arjenhiemstra/ithowifi/images/itho pcb w add-on.png

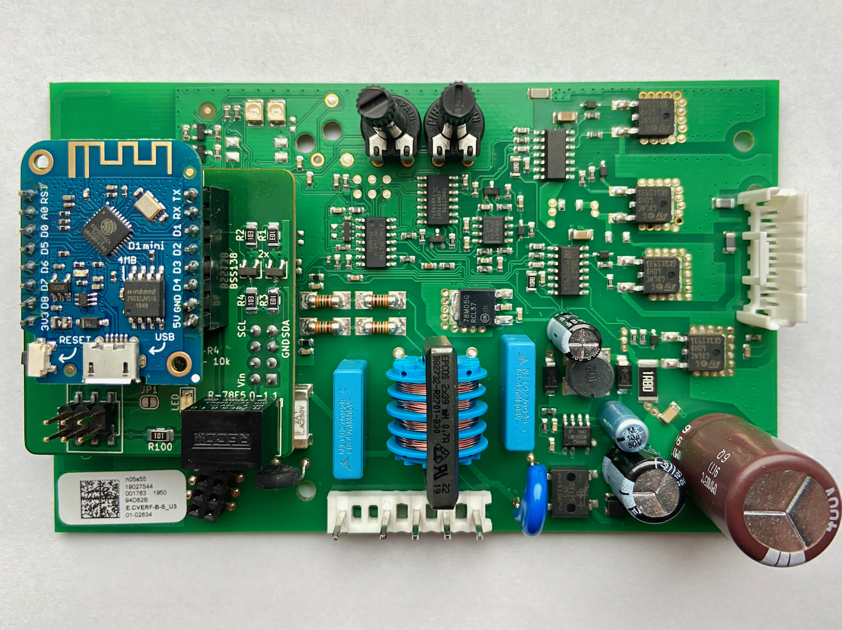
images/itho pcb w add-on.png
