arjenhiemstra/ithowifi/images/itho pcb.png

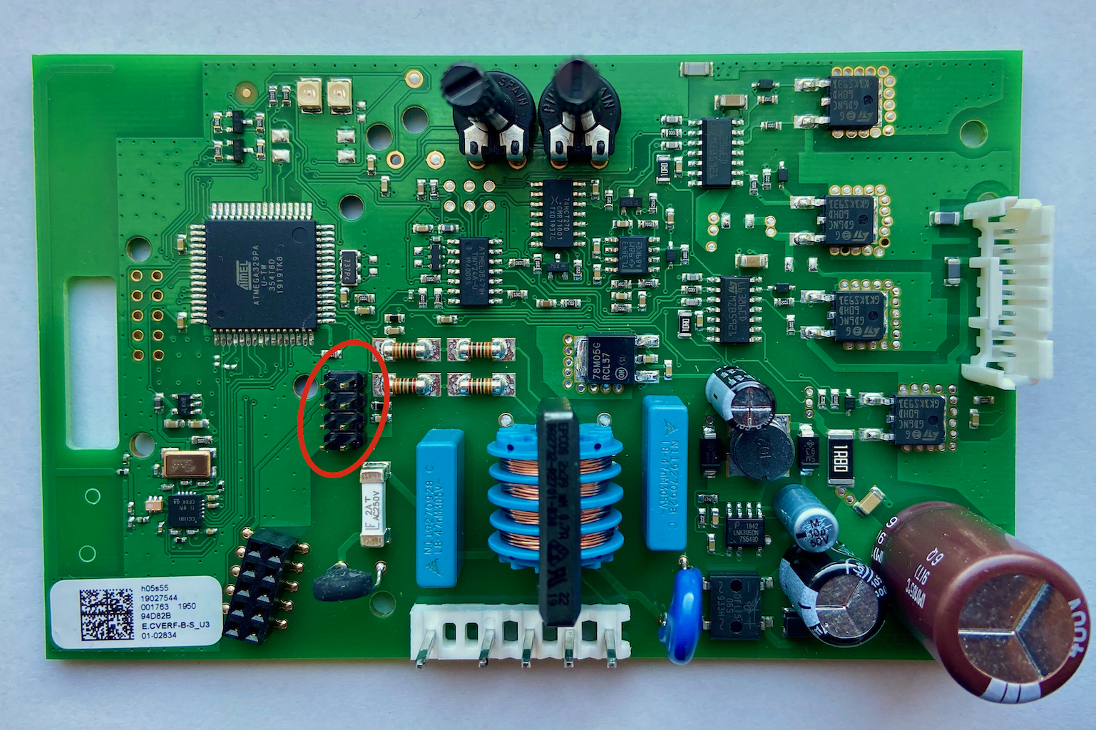
images/itho pcb.png
