arjenhiemstra/ithowifi/images/wiki/HRU pins.jpg

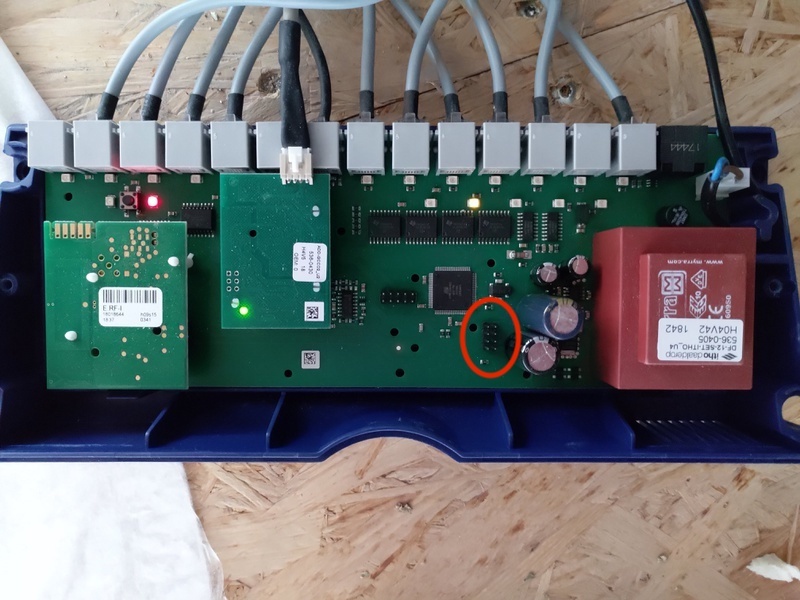
images/wiki/HRU pins.jpg
