arjenhiemstra/ithowifi/images/wiki/itho_grey_box.jpg

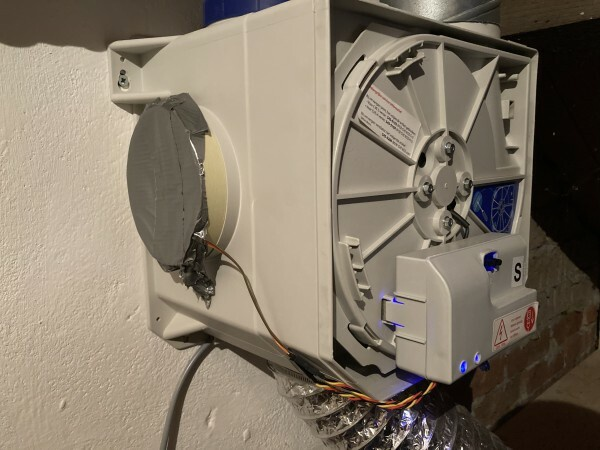
images/wiki/itho_grey_box.jpg
