arjenhiemstra/ithowifi/images/wiki/itho_in_blue_box.jpg

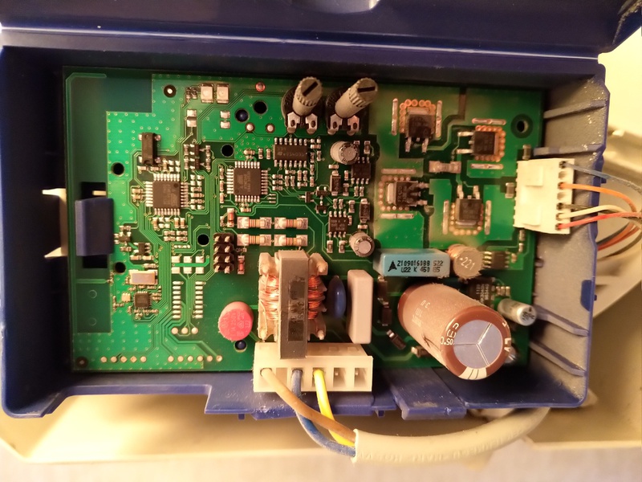
images/wiki/itho_in_blue_box.jpg
