arjenhiemstra/ithowifi/images/wiki/itho_RV_through-hole-box.jpg

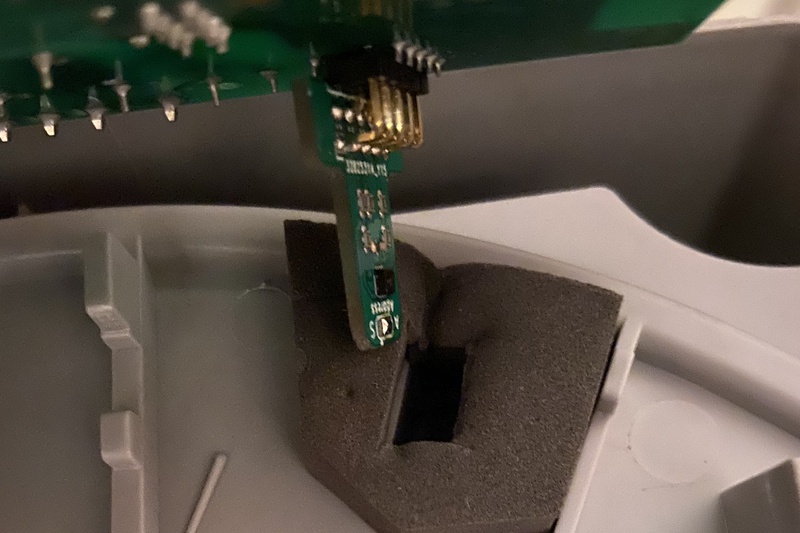
images/wiki/itho_RV_through-hole-box.jpg
