arjenhiemstra/ithowifi/images/wiki/join command.jpg

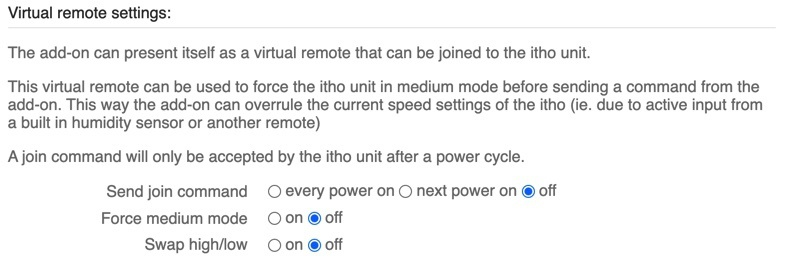
images/wiki/join command.jpg
