arjenhiemstra/ithowifi/images/wiki/pcb.png

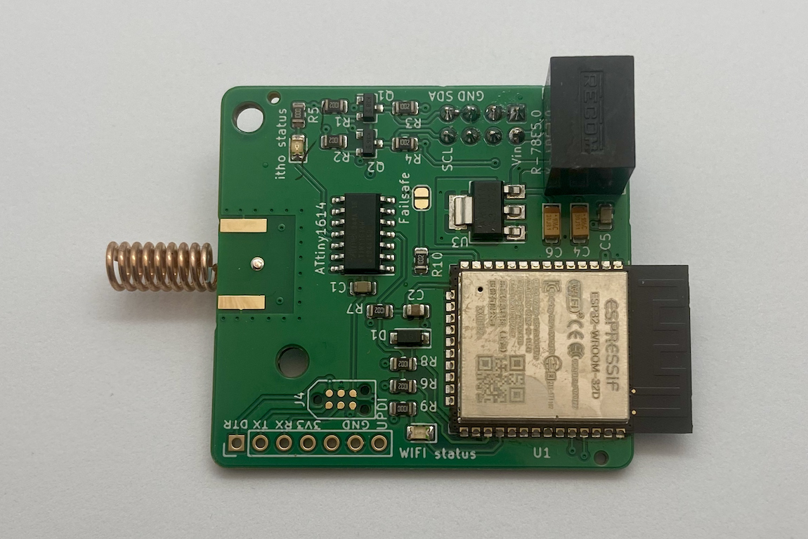
images/wiki/pcb.png
