arjenhiemstra/ithowifi/images/wiki/pinout rv sensor.png

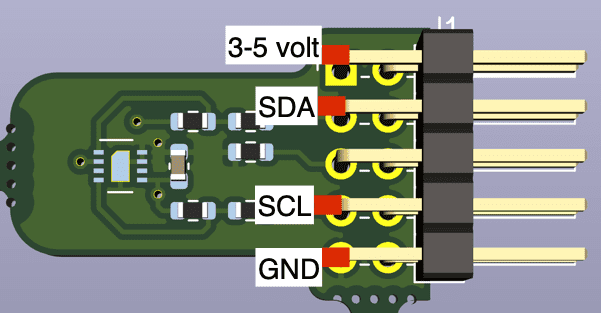
images/wiki/pinout rv sensor.png
