arjenhiemstra/ithowifi/images/wiki/Possible RV location2.jpg

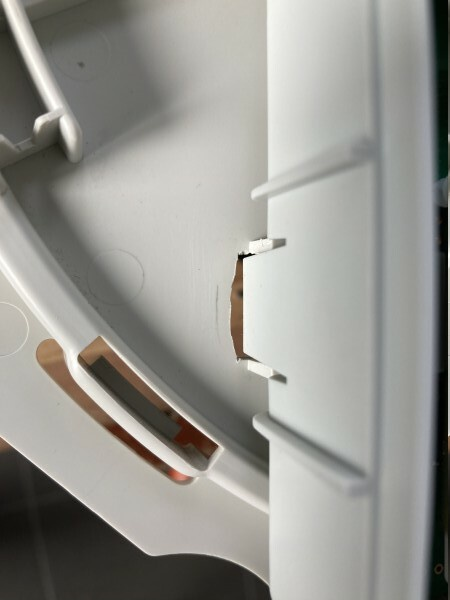
images/wiki/Possible RV location2.jpg
