arjenhiemstra/ithowifi/images/wiki/Possible RV location3.jpg

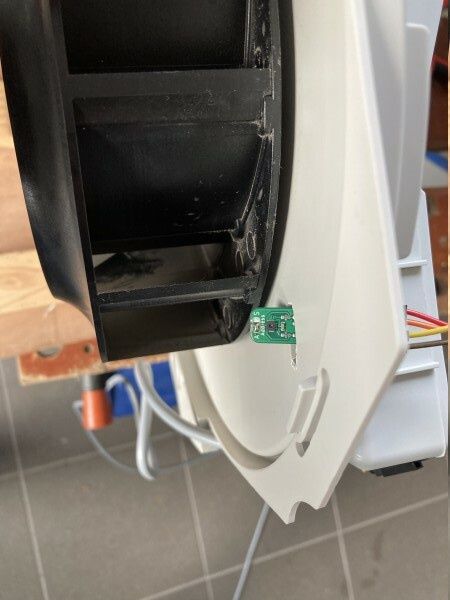
images/wiki/Possible RV location3.jpg
