arjenhiemstra/ithowifi/images/wiki/Possible RV location4.jpg

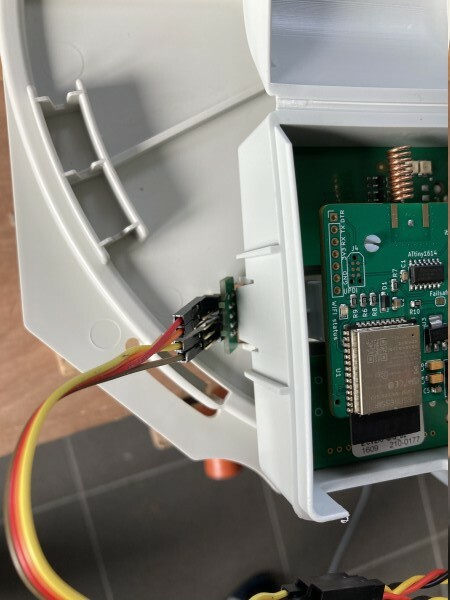
images/wiki/Possible RV location4.jpg
