arjenhiemstra/ithowifi/images/wiki/Remote 1.jpg

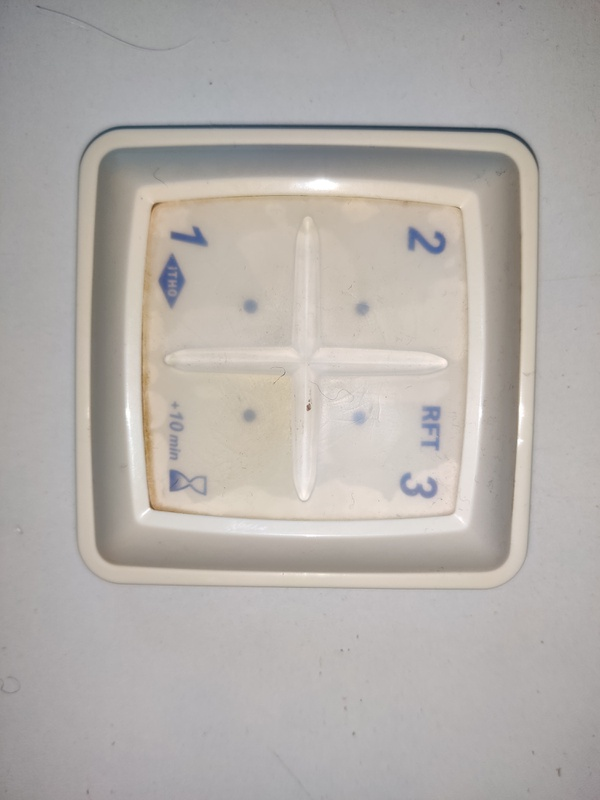
images/wiki/Remote 1.jpg
