arjenhiemstra/ithowifi/images/wiki/Remote 1_inside_bottom.jpg

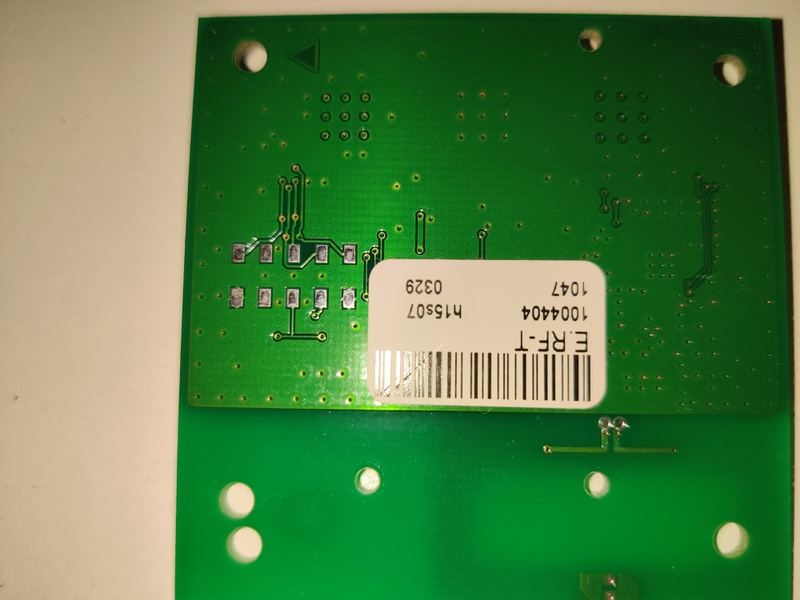
images/wiki/Remote 1_inside_bottom.jpg
