arjenhiemstra/ithowifi/images/wiki/Remote 1_inside_top.jpg

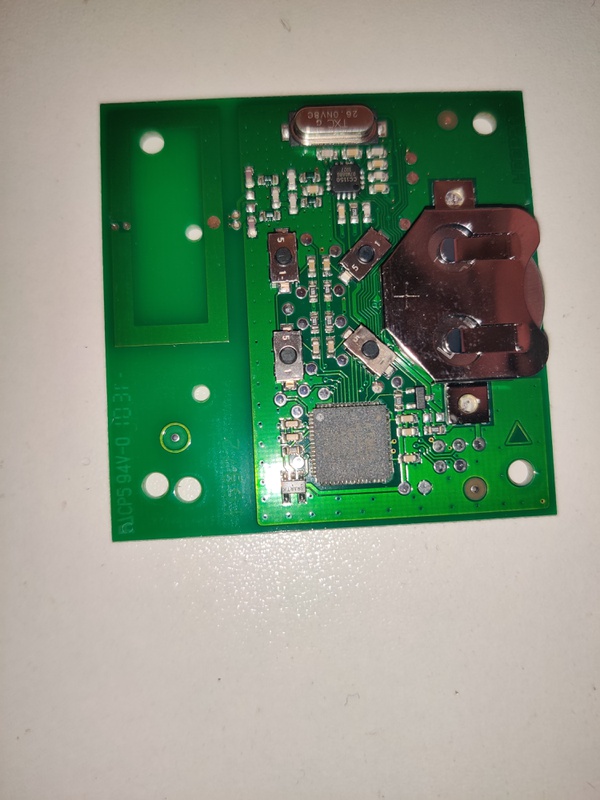
images/wiki/Remote 1_inside_top.jpg
