arjenhiemstra/ithowifi/images/wiki/Remote 2.jpg

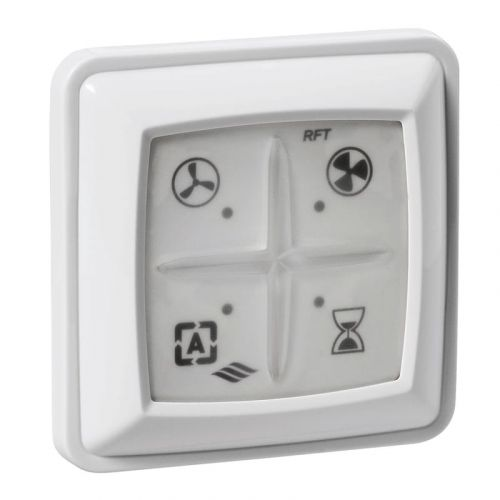
images/wiki/Remote 2.jpg
