arjenhiemstra/ithowifi/images/wiki/RV (org left) replacement (right).jpg

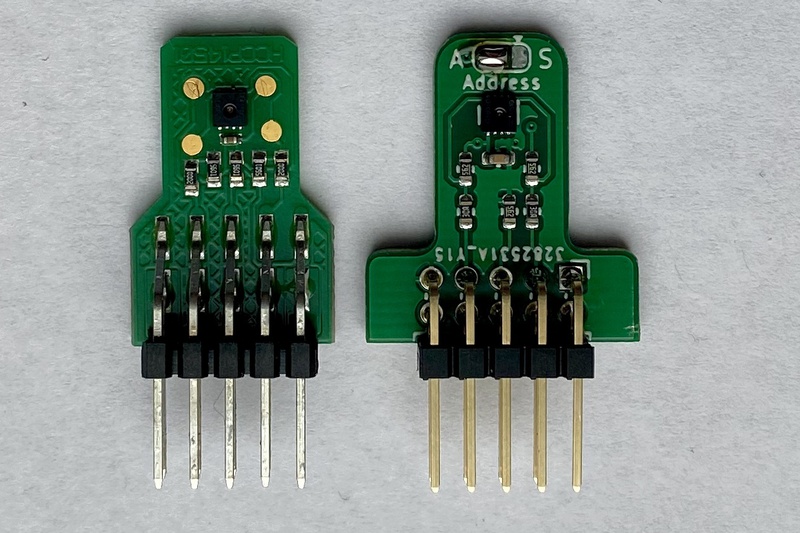
images/wiki/RV (org left) replacement (right).jpg
