arjenhiemstra/ithowifi/images/wiki/RV_bottom_side.jpg

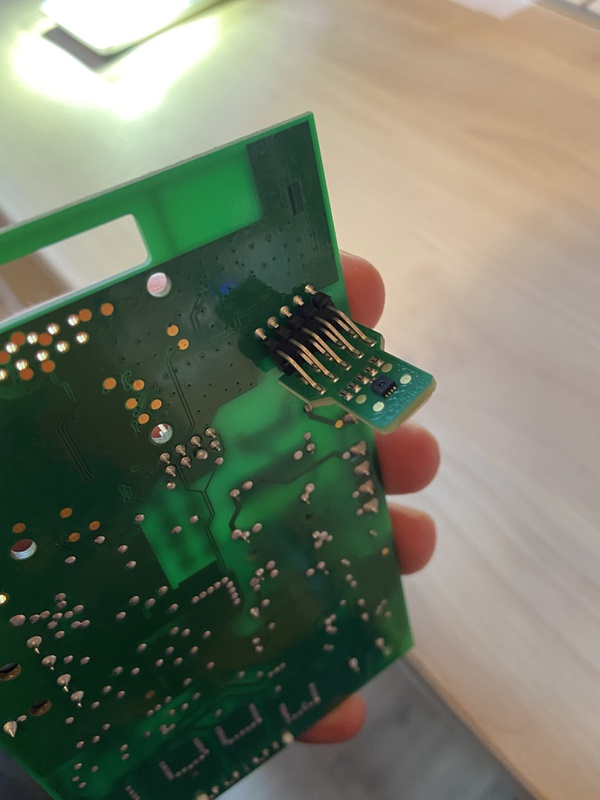
images/wiki/RV_bottom_side.jpg
