arjenhiemstra/ithowifi/images/wiki/speedsetting fan software.jpg

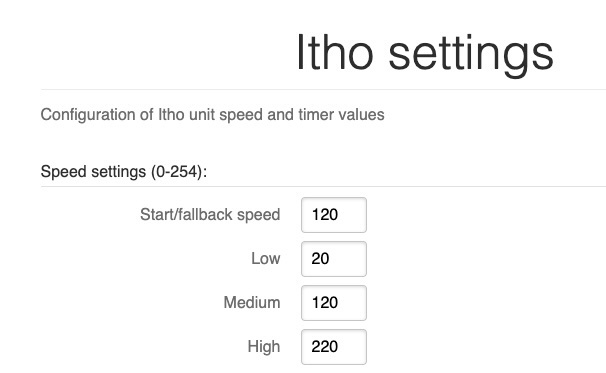
images/wiki/speedsetting fan software.jpg
