arjenhiemstra/ithowifi/images/wiki/sticker_from Factory.jpg

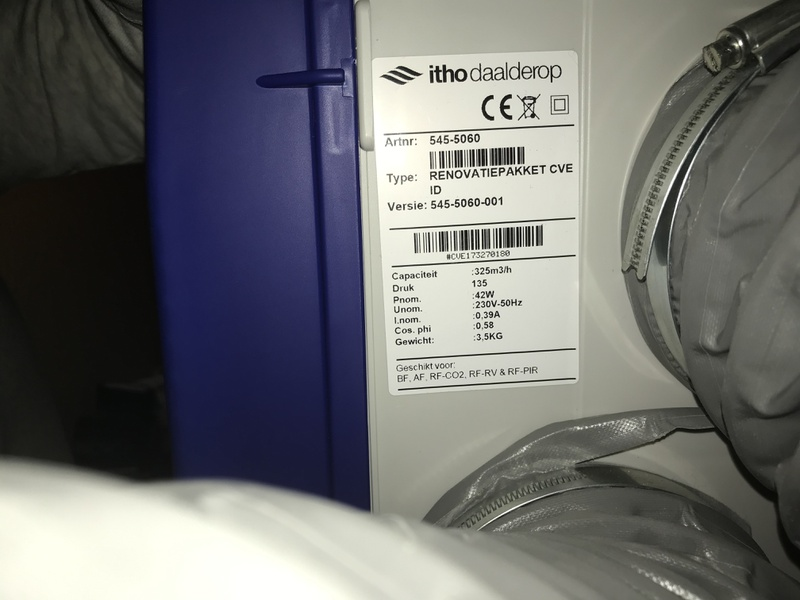
images/wiki/sticker_from Factory.jpg
