arjenhiemstra/ithowifi/images/wiki/tem_hum_connected via jumpercable.jpg

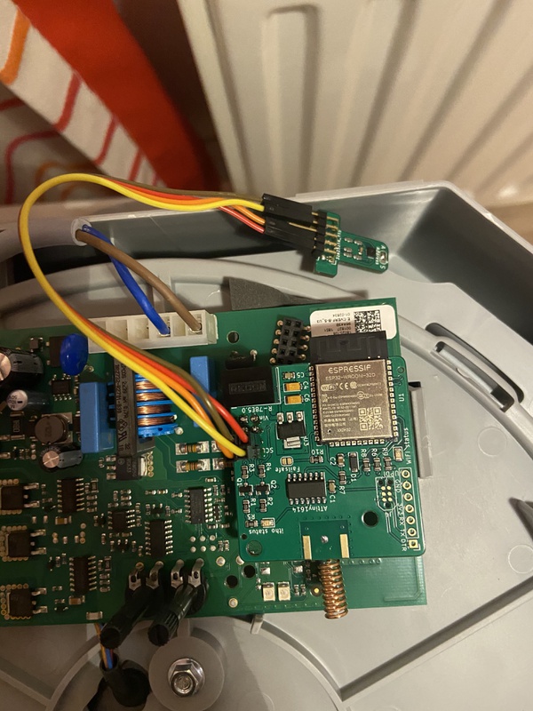
images/wiki/tem_hum_connected via jumpercable.jpg
