arjenhiemstra/ithowifi/images/wiki/webinterface_mainpage.png

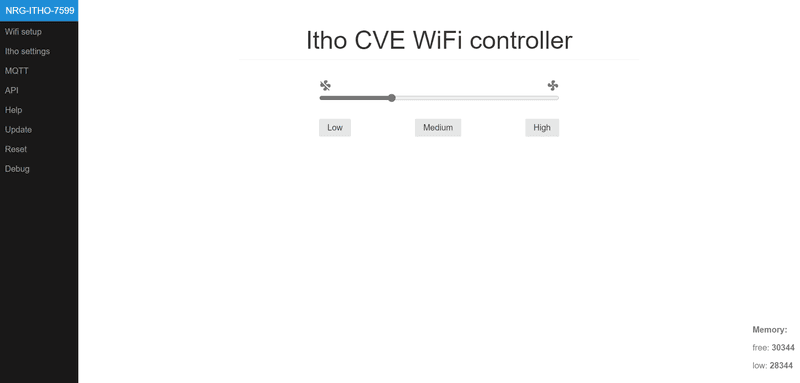
images/wiki/webinterface_mainpage.png
