arjenhiemstra/ithowifi/images/wiki/webinterface_mqtt_menu.png

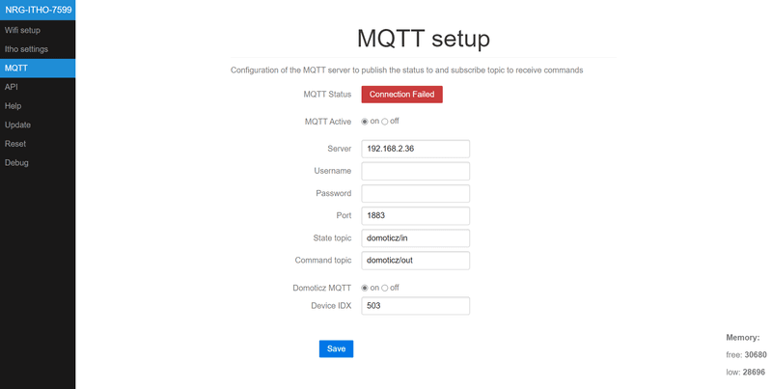
images/wiki/webinterface_mqtt_menu.png
