arjenhiemstra/ithowifi/remotes/536-0020.png

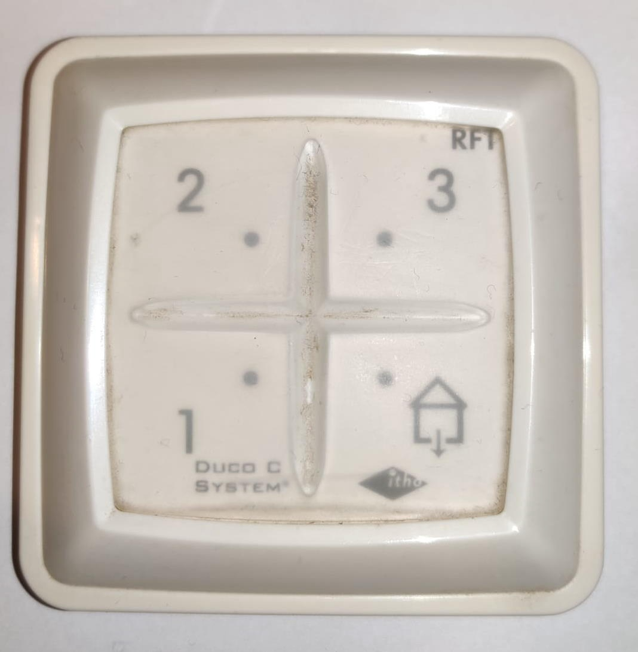
remotes/536-0020.png
