arjenhiemstra/ithowifi/remotes/536-0024.png

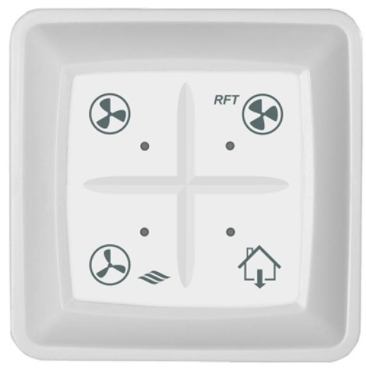
remotes/536-0024.png
