arjenhiemstra/ithowifi/remotes/536-0146.png

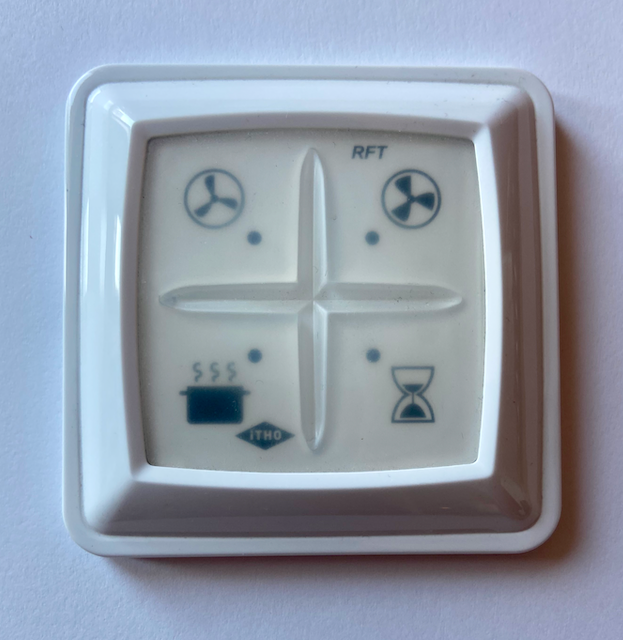
remotes/536-0146.png
