arjenhiemstra/ithowifi/remotes/remote1.png

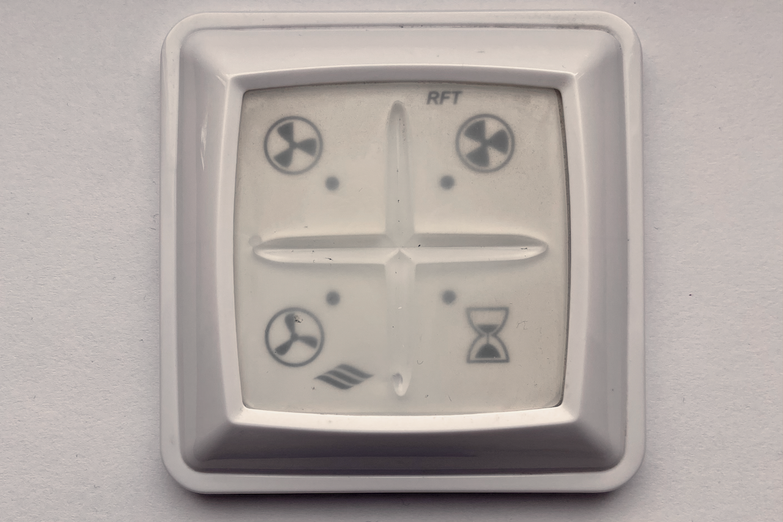
remotes/remote1.png
