arjenhiemstra/ithowifi/remotes/remote2.png

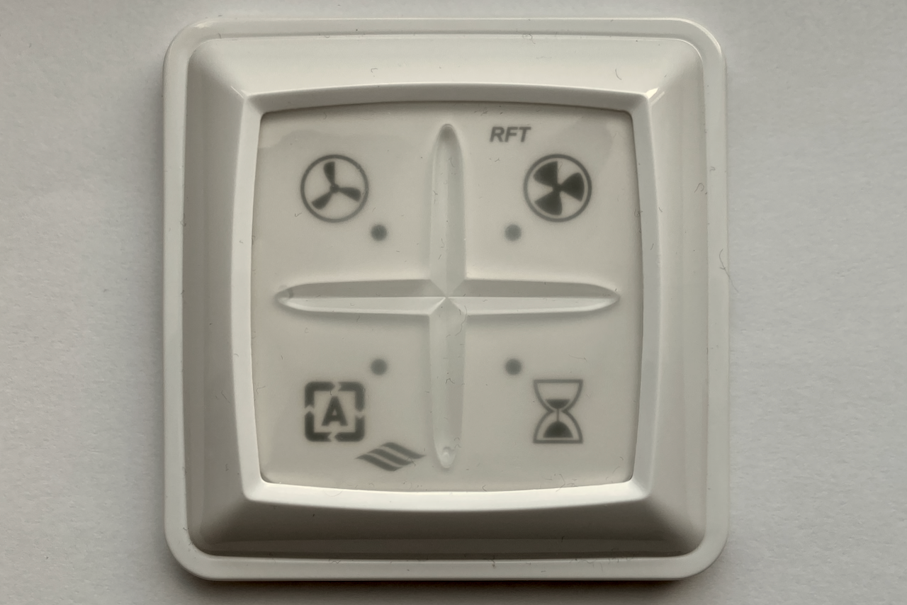
remotes/remote2.png
