arjenhiemstra/ithowifi/manual/wizard_images/autotemp.jpg

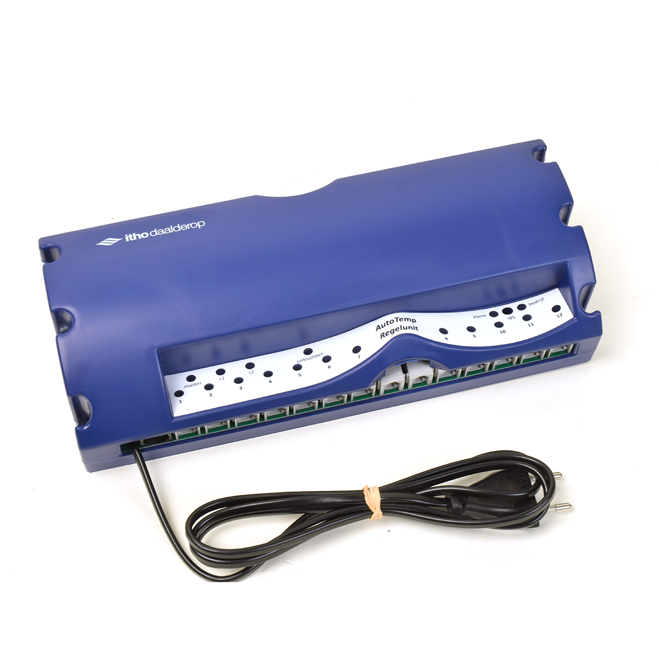
manual/wizard_images/autotemp.jpg
