arjenhiemstra/ithowifi/manual/wizard_images/cve.jpg

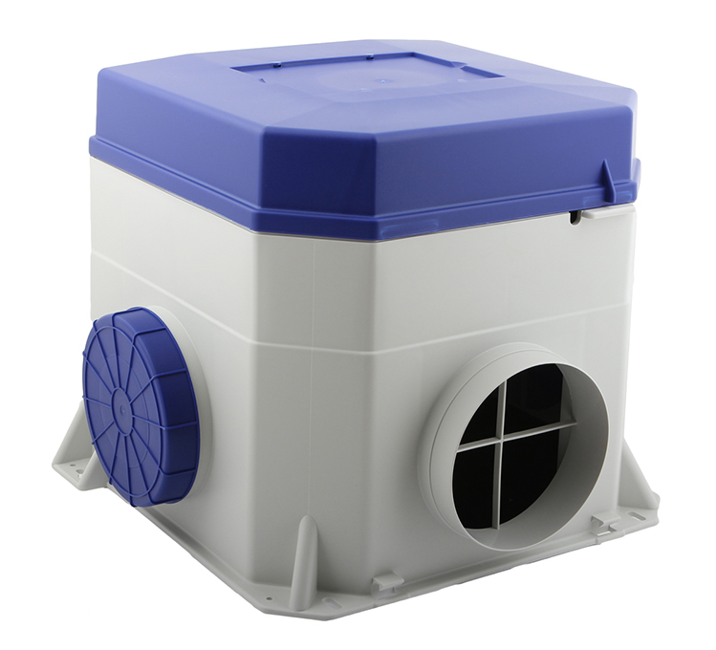
manual/wizard_images/cve.jpg
