arjenhiemstra/ithowifi/manual/wizard_images/cves.jpg

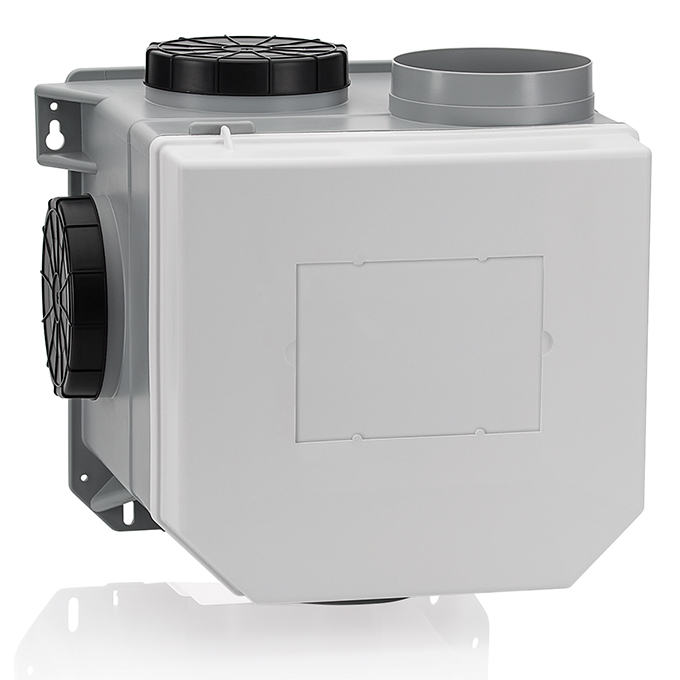
manual/wizard_images/cves.jpg
