arjenhiemstra/ithowifi/manual/wizard_images/demandflow.jpg

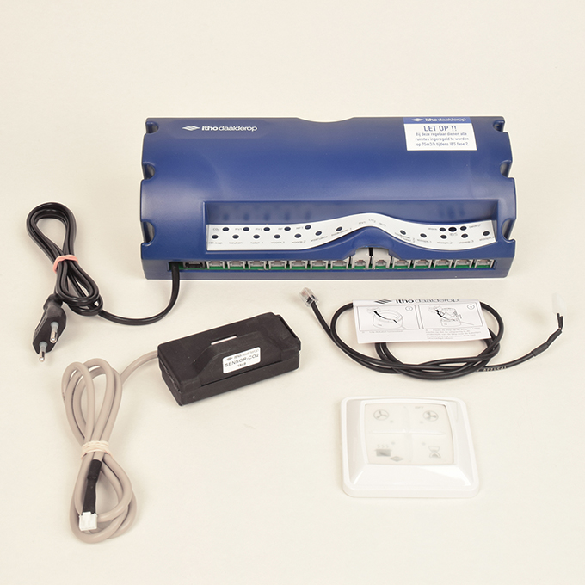
manual/wizard_images/demandflow.jpg
