arjenhiemstra/ithowifi/manual/wizard_images/hru150.jpg

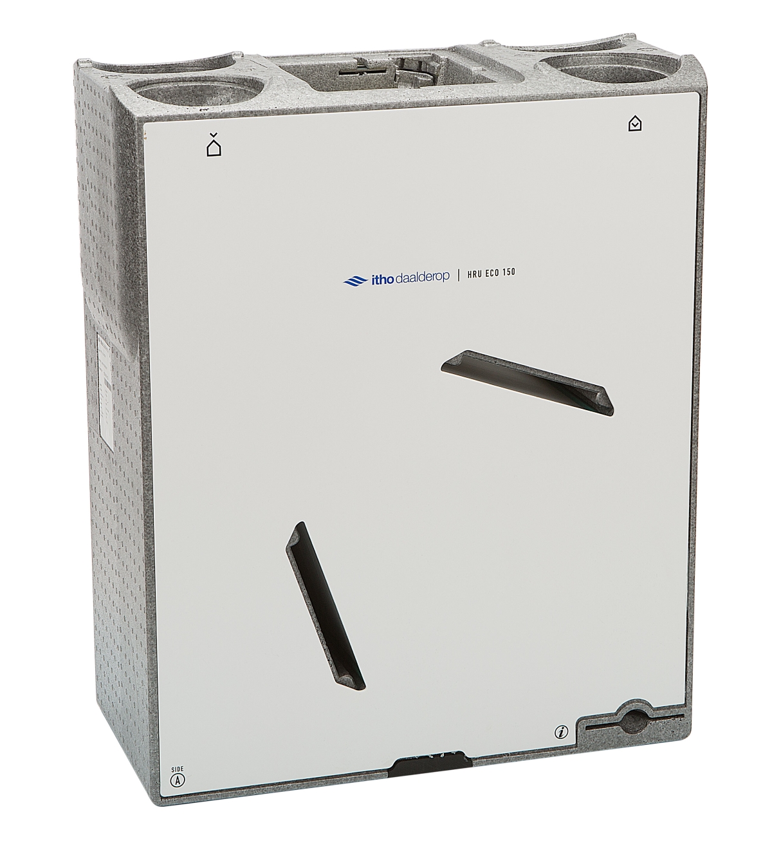
manual/wizard_images/hru150.jpg
