arjenhiemstra/ithowifi/manual/wizard_images/hru200.png

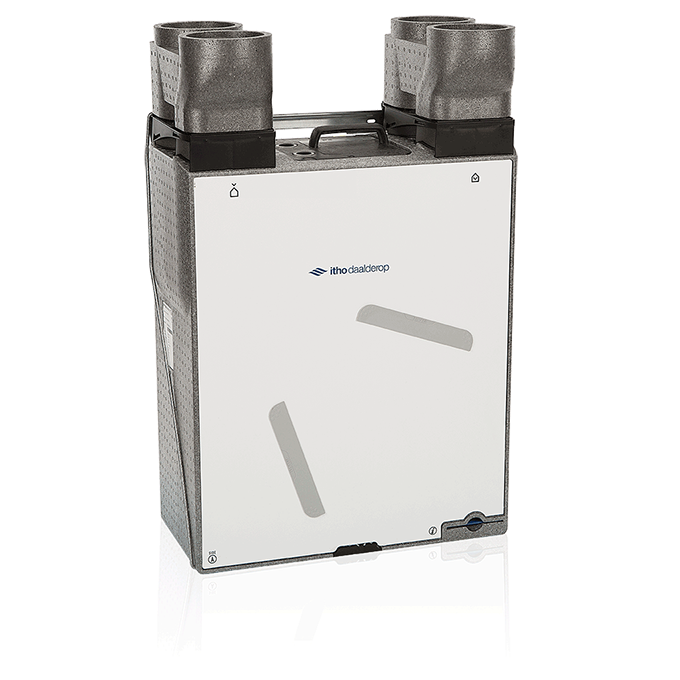
manual/wizard_images/hru200.png
