arjenhiemstra/ithowifi/manual/wizard_images/hru250_300_p_r.png

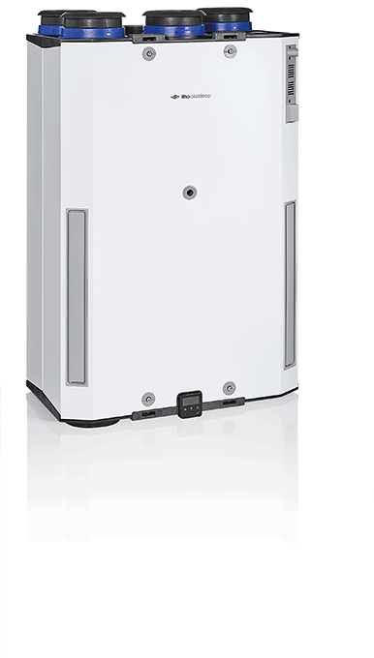
manual/wizard_images/hru250_300_p_r.png
