arjenhiemstra/ithowifi/manual/wizard_images/hru300v.jpg

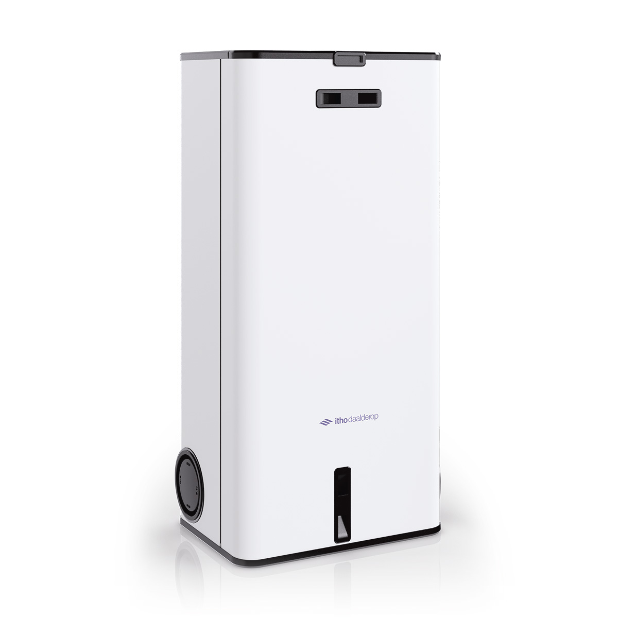
manual/wizard_images/hru300v.jpg
