arjenhiemstra/ithowifi/manual/wizard_images/hru350.png

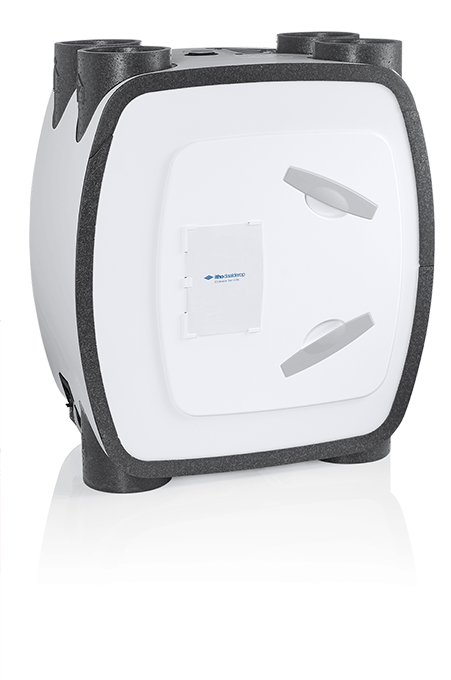
manual/wizard_images/hru350.png
