arjenhiemstra/ithowifi/manual/wizard_images/hru400.png

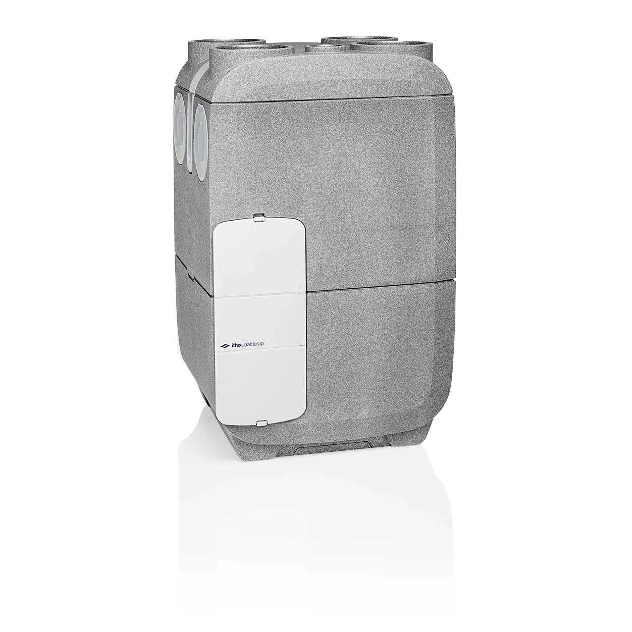
manual/wizard_images/hru400.png
