arjenhiemstra/ithowifi/manual/wizard_images/hrueco.jpg

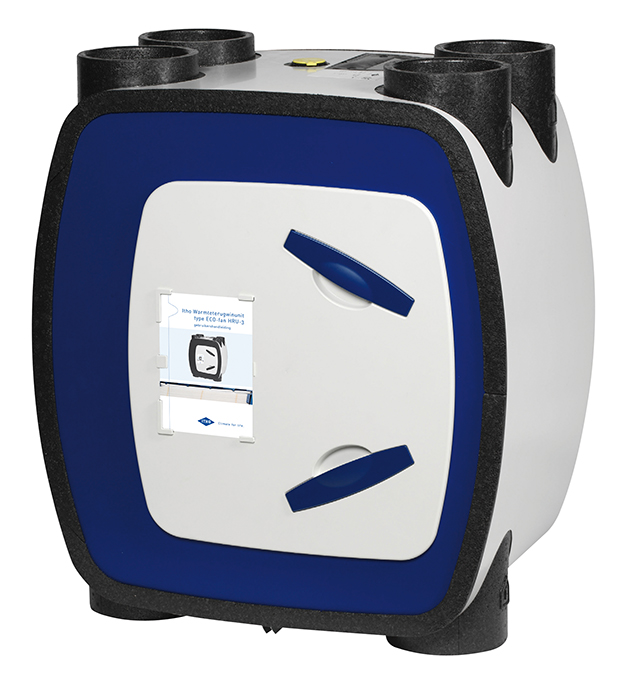
manual/wizard_images/hrueco.jpg
