arjenhiemstra/ithowifi/manual/wizard_images/wpu4g.jpg

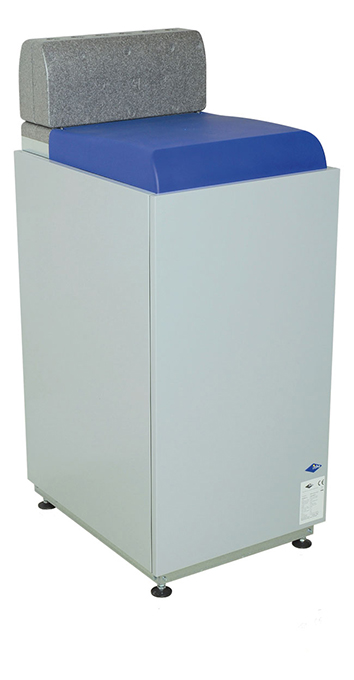
manual/wizard_images/wpu4g.jpg
