arjenhiemstra/ithowifi/manual/wizard_images/wpu5g.jpg

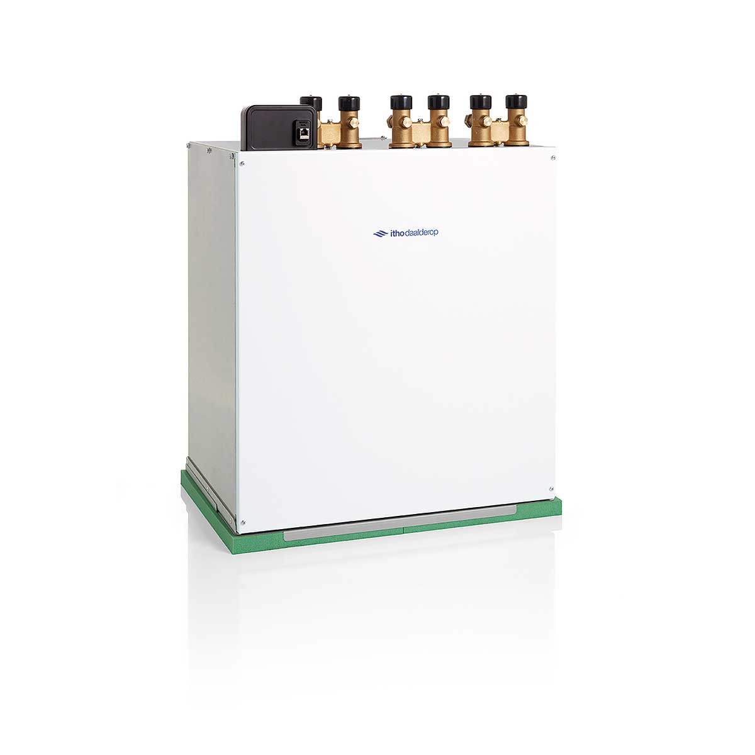
manual/wizard_images/wpu5g.jpg
