arjenhiemstra/ithowifi/software/NRG_itho_wifi/main/SHTSensor.cpp

/*
 *  Copyright (c) 2018, Sensirion AG <andreas.brauchli@sensirion.com>
 *  Copyright (c) 2015-2016, Johannes Winkelmann <jw@smts.ch>
 *  All rights reserved.
 *
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
 *  THIS SOFTWARE IS PROVIDED BY THE COPYRIGHT HOLDERS AND CONTRIBUTORS "AS IS"
 *  AND ANY EXPRESS OR IMPLIED WARRANTIES, INCLUDING, BUT NOT LIMITED TO, THE
 *  IMPLIED WARRANTIES OF MERCHANTABILITY AND FITNESS FOR A PARTICULAR PURPOSE
 *  ARE DISCLAIMED. IN NO EVENT SHALL <COPYRIGHT HOLDER> BE LIABLE FOR ANY
 *  DIRECT, INDIRECT, INCIDENTAL, SPECIAL, EXEMPLARY, OR CONSEQUENTIAL DAMAGES
 *  (INCLUDING, BUT NOT LIMITED TO, PROCUREMENT OF SUBSTITUTE GOODS OR SERVICES;
 *  LOSS OF USE, DATA, OR PROFITS; OR BUSINESS INTERRUPTION) HOWEVER CAUSED AND
 *  ON ANY THEORY OF LIABILITY, WHETHER IN CONTRACT, STRICT LIABILITY, OR TORT
 *  (INCLUDING NEGLIGENCE OR OTHERWISE) ARISING IN ANY WAY OUT OF THE USE OF
 *  THIS SOFTWARE, EVEN IF ADVISED OF THE POSSIBILITY OF SUCH DAMAGE.
 */

#include "SHTSensor.h"

//
// class SHTSensorDriver
//

SHTSensorDriver::~SHTSensorDriver()
{
}

bool SHTSensorDriver::readSample()
{
  return false;
}

//
// class SHTI2cSensor
//

const uint8_t SHTI2cSensor::CMD_SIZE = 2;
const uint8_t SHTI2cSensor::EXPECTED_DATA_SIZE = 6;

bool SHTI2cSensor::readFromI2c(uint8_t i2cAddress,
                               const uint8_t *i2cCommand,
                               uint8_t commandLength, uint8_t *data,
                               uint8_t dataLength,
                               uint8_t duration)
{

  if (!i2cSendCmd(i2cAddress, i2cCommand, commandLength, I2C_CMD_TEMP_READ_CMD))
  {
    return false;
  }

  delay(duration);

  i2cMasterReadSlave(i2cAddress, data, dataLength, I2C_CMD_TEMP_READ_SLAVE);

  return true;
}

uint8_t SHTI2cSensor::crc8(const uint8_t *data, uint8_t len)
{
  // adapted from SHT21 sample code from
  // http://www.sensirion.com/en/products/humidity-temperature/download-center/

  uint8_t crc = 0xff;
  uint8_t byteCtr;
  for (byteCtr = 0; byteCtr < len; ++byteCtr)
  {
    crc ^= data[byteCtr];
    for (uint8_t bit = 8; bit > 0; --bit)
    {
      if (crc & 0x80)
      {
        crc = (crc << 1) ^ 0x31;
      }
      else
      {
        crc = (crc << 1);
      }
    }
  }
  return crc;
}

bool SHTI2cSensor::readSample()
{
  uint8_t data[EXPECTED_DATA_SIZE];
  uint8_t cmd[CMD_SIZE];

  cmd[0] = mI2cCommand >> 8;
  cmd[1] = mI2cCommand & 0xff;

  if (!readFromI2c(mI2cAddress, cmd, CMD_SIZE, data,
                   EXPECTED_DATA_SIZE, mDuration))
  {
    return false;
  }

  // -- Important: assuming each 2 byte of data is followed by 1 byte of CRC

  // check CRC for both RH and T
  if (crc8(&data[0], 2) != data[2] || crc8(&data[3], 2) != data[5])
  {
    return false;
  }

  // convert to Temperature/Humidity
  uint16_t val;
  val = (data[0] << 8) + data[1];
  mTemperature = mA + mB * (val / mC);

  val = (data[3] << 8) + data[4];
  mHumidity = mX * (val / mY);

  return true;
}


//
// class SHTC1Sensor
//

class SHTC1Sensor : public SHTI2cSensor
{
public:
  SHTC1Sensor()
      // clock stretching disabled, high precision, T first
      : SHTI2cSensor(0x70, 0x7866, 15, -45, 175, 65535, 100, 65535)
  {
  }
};

//
// class SHT3xSensor
//

class SHT3xSensor : public SHTI2cSensor
{
private:
  static const uint16_t SHT3X_ACCURACY_HIGH = 0x2400;
  static const uint16_t SHT3X_ACCURACY_MEDIUM = 0x240b;
  static const uint16_t SHT3X_ACCURACY_LOW = 0x2416;

  static const uint8_t SHT3X_ACCURACY_HIGH_DURATION = 15;
  static const uint8_t SHT3X_ACCURACY_MEDIUM_DURATION = 6;
  static const uint8_t SHT3X_ACCURACY_LOW_DURATION = 4;

public:
  static const uint8_t SHT3X_I2C_ADDRESS_44 = 0x44;
  static const uint8_t SHT3X_I2C_ADDRESS_45 = 0x45;

  SHT3xSensor(uint8_t i2cAddress = SHT3X_I2C_ADDRESS_44)
      : SHTI2cSensor(i2cAddress, SHT3X_ACCURACY_HIGH,
                     SHT3X_ACCURACY_HIGH_DURATION,
                     -45, 175, 65535, 100, 65535)
  {
  }

  virtual bool setAccuracy(SHTSensor::SHTAccuracy newAccuracy)
  {
    switch (newAccuracy)
    {
    case SHTSensor::SHT_ACCURACY_HIGH:
      mI2cCommand = SHT3X_ACCURACY_HIGH;
      mDuration = SHT3X_ACCURACY_HIGH_DURATION;
      break;
    case SHTSensor::SHT_ACCURACY_MEDIUM:
      mI2cCommand = SHT3X_ACCURACY_MEDIUM;
      mDuration = SHT3X_ACCURACY_MEDIUM_DURATION;
      break;
    case SHTSensor::SHT_ACCURACY_LOW:
      mI2cCommand = SHT3X_ACCURACY_LOW;
      mDuration = SHT3X_ACCURACY_LOW_DURATION;
      break;
    default:
      return false;
    }
    return true;
  }

  virtual bool softReset()
  {
    /*
    from: Sensirion_Humidity_Sensors_SHT3x_Datasheet_digital.pdf
    Interface Reset
      If communication with the device is lost, the following
      signal sequence will reset the serial interface: While
      leaving SDA high, toggle SCL nine or more times. This
      must be followed by a Transmission Start sequence
      preceding the next command. This sequence resets the
      interface only. The status register preserves its content.
    */
    // Remove any existing I2C drivers
    i2cMasterDeinit();
    i2cSlaveDeinit();

    pinMode(i2cManager.master_sda_pin, OUTPUT); // Make SDA (data) and SCL (clock) pins outputs
    pinMode(i2cManager.master_scl_pin, OUTPUT);

    digitalWrite(i2cManager.master_sda_pin, HIGH);
    digitalWrite(i2cManager.master_scl_pin, HIGH);

    for (uint i = 0; i < 9; i++)
    {
      digitalWrite(i2cManager.master_scl_pin, LOW);
      delayMicroseconds(10);
      digitalWrite(i2cManager.master_scl_pin, HIGH);
      delayMicroseconds(10);
    }

    pinMode(i2cManager.master_sda_pin, INPUT); // and reset pins as tri-state inputs which is the default state on reset
    pinMode(i2cManager.master_scl_pin, INPUT);

    delayMicroseconds(20);

    if (!readSample())
      return false;

    return true;
  }
};

//
// class SHT3xAnalogSensor
//

float SHT3xAnalogSensor::readHumidity()
{
  float max_adc = (float)((1 << mReadResolutionBits) - 1);
  return -12.5f + 125 * (analogRead(mHumidityAdcPin) / max_adc);
}

float SHT3xAnalogSensor::readTemperature()
{
  float max_adc = (float)((1 << mReadResolutionBits) - 1);
  return -66.875f + 218.75f * (analogRead(mTemperatureAdcPin) / max_adc);
}

//
// class SHTSensor
//

const SHTSensor::SHTSensorType SHTSensor::AUTO_DETECT_SENSORS[] = {
    SHT3X,
    SHT3X_ALT,
    SHTC1};
const float SHTSensor::TEMPERATURE_INVALID = NAN;
const float SHTSensor::HUMIDITY_INVALID = NAN;

bool SHTSensor::init()
{
  if (mSensor != NULL)
  {
    cleanup();
  }

  switch (mSensorType)
  {
  case SHT3X:
    mSensor = new SHT3xSensor();
    break;

  case SHT3X_ALT:
    mSensor = new SHT3xSensor(SHT3xSensor::SHT3X_I2C_ADDRESS_45);
    break;

  case SHTW1:
  case SHTW2:
  case SHTC1:
    mSensor = new SHTC1Sensor();
    break;

  case AUTO_DETECT:
  {
    bool detected = false;
    for (unsigned int i = 0;
         i < sizeof(AUTO_DETECT_SENSORS) / sizeof(AUTO_DETECT_SENSORS[0]);
         ++i)
    {
      mSensorType = AUTO_DETECT_SENSORS[i];
      if (init() && readSample())
      {
        detected = true;
        break;
      }
    }
    if (!detected)
    {
      cleanup();
    }
    break;
  }
  }
  return (mSensor != NULL);
}

bool SHTSensor::readSample()
{
  if (!mSensor || !mSensor->readSample())
    return false;
  mTemperature = mSensor->mTemperature;
  mHumidity = mSensor->mHumidity;
  return true;
}

bool SHTSensor::setAccuracy(SHTAccuracy newAccuracy)
{
  if (!mSensor)
    return false;
  return mSensor->setAccuracy(newAccuracy);
}

bool SHTSensor::softReset()
{
  if (!mSensor)
    return false;
  return mSensor->softReset();
}

void SHTSensor::cleanup()
{
  if (mSensor)
  {
    delete mSensor;
    mSensor = NULL;
  }
}
