arjenhiemstra/ithowifi/software/NRG_itho_wifi/main/generic_functions.cpp

#include "generic_functions.h"
#include "config/HADiscConfig.h"
#include "tasks/task_cc1101.h"
#include <HTTPUpdate.h>

// MAX_FIRMWARE_HTTPS_RESPONSE_SIZE is normally injected by build_script.py based
// on the actual firmware.json size + headroom. This fallback only applies if the
// build flag wasn't set.
#ifndef MAX_FIRMWARE_HTTPS_RESPONSE_SIZE
#define MAX_FIRMWARE_HTTPS_RESPONSE_SIZE 16384
#endif

// locals
Ticker IthoCMD;
const char *espName = "nrg-itho-";

const char *getCurrentFanInfo()
{
  // Check I2C 31DA measurements first (freshest when itho_31da is enabled).
  if (xSemaphoreTake(ithoStatusMutex, pdMS_TO_TICKS(100)) == pdTRUE)
  {
    for (const auto &m : ithoMeasurements)
    {
      if (m.type == ithoDeviceMeasurements::is_string &&
          (strcmp(m.name, "FanInfo") == 0 || strcmp(m.name, "fan-info") == 0) &&
          m.value.stringval != nullptr)
      {
        const char *v = m.value.stringval;
        xSemaphoreGive(ithoStatusMutex);
        return v;
      }
    }
    xSemaphoreGive(ithoStatusMutex);
  }
  // Fall back to sniffed RF 31DA across any active+tracked source.
  for (int i = 0; i < MAX_RF_STATUS_SOURCES; i++)
  {
    if (!rfStatusSources[i].active || !rfStatusSources[i].tracked)
      continue;
    for (const auto &m : rfStatusSources[i].measurements31DA)
    {
      if (m.type == ithoDeviceMeasurements::is_string &&
          (strcmp(m.name, "FanInfo") == 0 || strcmp(m.name, "fan-info") == 0) &&
          m.value.stringval != nullptr)
      {
        return m.value.stringval;
      }
    }
  }
  return nullptr;
}

bool fanIsInAuto()
{
  const char *fi = getCurrentFanInfo();
  return fi != nullptr && strcmp(fi, "auto") == 0;
}

volatile uint16_t nextIthoVal = 0;
volatile unsigned long nextIthoTimer = 0;

const char *hostName()
{
  static char hostName[32]{};

  if (strcmp(wifiConfig.hostname, "") == 0)
  {
    snprintf(hostName, sizeof(hostName), "%s%02x%02x", espName, sys.getMac(4), sys.getMac(5));
  }
  else
  {
    strlcpy(hostName, wifiConfig.hostname, sizeof(hostName));
  }

  return hostName;
}

uint8_t getIthoStatusJSON(JsonObject root)
{
  uint8_t index = 0;
  if (SHT3x_original || SHT3x_alternative || itho_internal_hum_temp)
  {
    root["temp"] = round(ithoTemp, 1);
    index++;
    root["hum"] = round(ithoHum, 1);
    index++;
    auto b = 611.21 * pow(2.7183, ((18.678 - ithoTemp / 234.5) * ithoTemp) / (257.14 + ithoTemp));
    auto ppmw = b / (101325 - b) * ithoHum / 100 * 0.62145 * 1000000;
    root["ppmw"] = static_cast<int>(ppmw + 0.5);
    index++;
  }
  if (xSemaphoreTake(ithoStatusMutex, pdMS_TO_TICKS(100)) != pdTRUE)
    return index;
  if (!ithoInternalMeasurements.empty() && systemConfig.itho_31d9 == 1)
  {
    for (const auto &internalMeasurement : ithoInternalMeasurements)
    {
      if (internalMeasurement.type == ithoDeviceMeasurements::is_int)
      {
        root[internalMeasurement.name] = internalMeasurement.value.intval;
      }
      else if (internalMeasurement.type == ithoDeviceMeasurements::is_float)
      {
        root[internalMeasurement.name] = round(internalMeasurement.value.floatval, 2);
      }
      else
      {
        root["error"] = 0;
      }
      index++;
    }
  }
  if (!ithoMeasurements.empty() && systemConfig.itho_31da == 1)
  {
    for (const auto &ithoMeasurement : ithoMeasurements)
    {
      if (ithoMeasurement.type == ithoDeviceMeasurements::is_int)
      {
        root[ithoMeasurement.name] = ithoMeasurement.value.intval;
      }
      else if (ithoMeasurement.type == ithoDeviceMeasurements::is_float)
      {
        root[ithoMeasurement.name] = round(ithoMeasurement.value.floatval, 2);
      }
      else if (ithoMeasurement.type == ithoDeviceMeasurements::is_string)
      {
        root[ithoMeasurement.name] = ithoMeasurement.value.stringval;
      }
      index++;
    }
  }
  if (!ithoStatus.empty() && systemConfig.itho_2401 == 1)
  {
    for (const auto &ithoStat : ithoStatus)
    {
      if (ithoStat.type == ithoDeviceStatus::is_byte)
      {
        root[ithoStat.name] = ithoStat.value.byteval;
      }
      else if (ithoStat.type == ithoDeviceStatus::is_int)
      {
        root[ithoStat.name] = ithoStat.value.intval;
      }
      else if (ithoStat.type == ithoDeviceStatus::is_float)
      {
        root[ithoStat.name] = round(ithoStat.value.floatval, 2);
      }
      else if (ithoStat.type == ithoDeviceStatus::is_string)
      {
        root[ithoStat.name] = ithoStat.value.stringval;
      }
      index++;
    }
  }
  if (!ithoCounters.empty() && systemConfig.itho_4210 == 1)
  {
    for (const auto &Counter : ithoCounters)
    {
      if (Counter.type == ithoDeviceMeasurements::is_int)
      {
        root[Counter.name] = Counter.value.intval;
      }
      else if (Counter.type == ithoDeviceMeasurements::is_float)
      {
        root[Counter.name] = round(Counter.value.floatval, 2);
      }
      else
      {
        root["error"] = 0;
      }
      index++;
    }
  }
  xSemaphoreGive(ithoStatusMutex);
  return index;
}

uint8_t getRFStatusJSON(JsonObject root, int sourceIndex, bool trackedOnly)
{
  uint8_t count = 0;

  JsonArray sources = root["sources"].to<JsonArray>();
  for (int i = 0; i < MAX_RF_STATUS_SOURCES; i++)
  {
    if (!rfStatusSources[i].active)
      continue;
    if (trackedOnly && !rfStatusSources[i].tracked)
      continue;
    JsonObject src = sources.add<JsonObject>();
    char idStr[10];
    snprintf(idStr, sizeof(idStr), "%02X:%02X:%02X",
             rfStatusSources[i].id[0], rfStatusSources[i].id[1], rfStatusSources[i].id[2]);
    src["id"] = idStr;
    src["index"] = i;
    src["lastSeen"] = static_cast<int32_t>(rfStatusSources[i].lastSeen);

    if (trackedOnly)
    {
      src["tracked"] = rfStatusSources[i].tracked;
      src["name"] = rfStatusSources[i].name;
      // Domain byte from the latest 31DA / 31D9 frame. 0 on single-zone
      // units; non-zero indicates a multi-zone HRU's zone ID (#366).
      src["zone31DA"] = rfStatusSources[i].lastZone31DA;
      src["zone31D9"] = rfStatusSources[i].lastZone31D9;
      JsonObject data = src["data"].to<JsonObject>();
      for (const auto &m : rfStatusSources[i].measurements31D9)
      {
        if (m.type == ithoDeviceMeasurements::is_int)
          data[m.name] = m.value.intval;
        else if (m.type == ithoDeviceMeasurements::is_float)
          data[m.name] = round(m.value.floatval, 2);
        else if (m.type == ithoDeviceMeasurements::is_string)
          data[m.name] = m.value.stringval;
        count++;
      }
      for (const auto &m : rfStatusSources[i].measurements31DA)
      {
        if (m.type == ithoDeviceMeasurements::is_int)
          data[m.name] = m.value.intval;
        else if (m.type == ithoDeviceMeasurements::is_float)
          data[m.name] = round(m.value.floatval, 2);
        else if (m.type == ithoDeviceMeasurements::is_string)
          data[m.name] = m.value.stringval;
        count++;
      }
    }
  }

  if (!trackedOnly)
  {
    int idx = sourceIndex;
    if (idx == -1)
    {
      for (int i = 0; i < MAX_RF_STATUS_SOURCES; i++)
      {
        if (rfStatusSources[i].active)
        {
          idx = i;
          break;
        }
      }
    }

    if (idx >= 0 && idx < MAX_RF_STATUS_SOURCES && rfStatusSources[idx].active)
    {
      root["selectedSource"] = idx;
      // See note above for trackedOnly path.
      root["zone31DA"] = rfStatusSources[idx].lastZone31DA;
      root["zone31D9"] = rfStatusSources[idx].lastZone31D9;
      JsonObject data = root["data"].to<JsonObject>();

      for (const auto &m : rfStatusSources[idx].measurements31D9)
      {
        if (m.type == ithoDeviceMeasurements::is_int)
          data[m.name] = m.value.intval;
        else if (m.type == ithoDeviceMeasurements::is_float)
          data[m.name] = round(m.value.floatval, 2);
        else if (m.type == ithoDeviceMeasurements::is_string)
          data[m.name] = m.value.stringval;
        count++;
      }

      for (const auto &m : rfStatusSources[idx].measurements31DA)
      {
        if (m.type == ithoDeviceMeasurements::is_int)
          data[m.name] = m.value.intval;
        else if (m.type == ithoDeviceMeasurements::is_float)
          data[m.name] = round(m.value.floatval, 2);
        else if (m.type == ithoDeviceMeasurements::is_string)
          data[m.name] = m.value.stringval;
        count++;
      }
    }
  }

  return count;
}

void getRFStatusConfigJSON(JsonObject root, int sourceIndex)
{
  JsonArray sources = root["sources"].to<JsonArray>();
  for (int i = 0; i < MAX_RF_STATUS_SOURCES; i++)
  {
    if (!rfStatusSources[i].active)
      continue;
    JsonObject src = sources.add<JsonObject>();
    char idStr[10];
    snprintf(idStr, sizeof(idStr), "%02X:%02X:%02X",
             rfStatusSources[i].id[0], rfStatusSources[i].id[1], rfStatusSources[i].id[2]);
    src["id"] = idStr;
    src["index"] = i;
    src["tracked"] = rfStatusSources[i].tracked;
    src["name"] = rfStatusSources[i].name;
  }

  int trackedCount = 0;
  for (int i = 0; i < MAX_RF_STATUS_SOURCES; i++)
    if (rfStatusSources[i].active && rfStatusSources[i].tracked)
      trackedCount++;
  root["trackedCount"] = trackedCount;
  root["maxTracked"] = MAX_RF_STATUS_SOURCES;

  int idx = sourceIndex;
  if (idx == -1)
  {
    for (int i = 0; i < MAX_RF_STATUS_SOURCES; i++)
    {
      if (rfStatusSources[i].active)
      {
        idx = i;
        break;
      }
    }
  }
  if (idx >= 0 && idx < MAX_RF_STATUS_SOURCES && rfStatusSources[idx].active)
    root["selectedSource"] = idx;
}

bool isPrereleaseVersion(const char *version)
{
  if (version == nullptr)
    return false;
  return strstr(version, "-beta") != nullptr ||
         strstr(version, "-rc") != nullptr ||
         strstr(version, "-alpha") != nullptr ||
         strstr(version, "-dev") != nullptr;
}

const char *getUpdateChannel()
{
  return isPrereleaseVersion(fw_version) ? "beta" : "stable";
}

void getDeviceInfoJSON(JsonObject root)
{
  root["itho_devtype"] = (systemConfig.itho_rf_standalone == 1 && strcmp(getIthoType(), "Unkown device type") == 0)
                             ? "Generic Itho device"
                             : getIthoType();
  root["itho_mfr"] = currentIthoDeviceGroup();
  root["itho_deviceid"] = currentIthoDeviceID();
  root["itho_hwversion"] = currentItho_hwversion();
  root["itho_fwversion"] = currentItho_fwversion();
  root["add-on_hwid"] = WiFi.macAddress();
  root["add-on_fwversion"] = fw_version;
  // OTA state for HA's update entity progress bar. otaUpdateProgress
  // semantics: -1=idle, 0-100=download/flash percentage, 101=done
  // (reboot pending), -2=error. The HA discovery val_tpl derives
  // in_progress / update_percentage from this single integer.
  root["ota_progress"] = static_cast<int>(otaUpdateProgress);
  root["itho_rf_standalone"] = systemConfig.itho_rf_standalone;
  root["itho_control_interface"] = systemConfig.itho_control_interface;
  if (systemConfig.fw_check)
  {
    root["add-on_fwupdate_available"] = firmwareInfo.fw_update_available == 1 ? "true" : "false";
    root["add-on_latest_fw"] = firmwareInfo.latest_fw;
    root["add-on_latest_beta_fw"] = firmwareInfo.latest_beta_fw;

    // Channel-aware fields for HA Auto Discovery: pick stable or beta
    // based on the running version, and clamp the reported "latest" to
    // the installed version when the channel target is empty or older.
    // This keeps HA's update entity quiet for beta users on the latest
    // beta and prevents spurious "downgrade" prompts.
    const char *channel = getUpdateChannel();
    const char *target = (strcmp(channel, "beta") == 0)
                             ? firmwareInfo.latest_beta_fw
                             : firmwareInfo.latest_fw;
    bool target_is_newer = strlen(target) > 0 &&
                           compareVersions(std::string(target), std::string(fw_version)) > 0;
    root["add-on_update_channel"] = channel;
    root["add-on_latest_for_channel"] = target_is_newer ? target : fw_version;
  }
}

bool ithoStatusReady()
{
  auto bp = [&](bool a, bool b)
  { return (a ? 1 : 0) | ((b ? 1 : 0) << 1); };

  if (xSemaphoreTake(ithoStatusMutex, pdMS_TO_TICKS(50)) != pdTRUE)
    return false;
  // Build itho_init_status as 2 bits per feature:
  itho_init_status =
      bp(systemConfig.itho_31d9 == 1, !ithoInternalMeasurements.empty())  // bits 0..1
      | (bp(systemConfig.itho_31da == 1, !ithoMeasurements.empty()) << 2) // bits 2..3
      | (bp(systemConfig.itho_2401 == 1, !ithoStatus.empty()) << 4)       // bits 4..5
      | (bp(systemConfig.itho_4210 == 1, !ithoCounters.empty()) << 6);    // bits 6..7
  xSemaphoreGive(ithoStatusMutex);

  // Check if any feature is “activated but not filled”
  for (int i = 0; i < 4; i++)
  {
    uint8_t p = (itho_init_status >> (2 * i)) & 3; // extract 2 bits
    if ((p & 1) && !(p & 2))
      return false; // bit0=activated, bit1=filled?
  }
  return true;
}

void getRemotesInfoJSON(JsonObject root)
{

  remotes.getCapabilities(root);
}

void getRFDevicesForHADiscJSON(JsonObject root)
{
  // Get list of RF devices with their available sensors for HA discovery configuration
  JsonArray devices = root["rfdevices"].to<JsonArray>();
  D_LOG("HAD: getRFDevicesForHADiscJSON:%d", remotes.getRemoteCount());

  for (int i = 0; i < remotes.getMaxRemotes(); i++)
  {
    if (remotes.isEmptySlot(i))
      continue;
    JsonObject device = devices.add<JsonObject>();
    device["idx"] = i;
    device["name"] = remotes.getRemoteNamebyIndex(i);
    uint16_t remType = static_cast<uint16_t>(remotes.getRemoteType(i));
    device["type"] = remType;
    device["available"] = HADiscConfig::getAvailableSensorsForType(remType);
    device["presets"] = HADiscConfig::getPresetsForType(remType);
  }
}

void getVirtualRemotesForHADiscJSON(JsonObject root)
{
  JsonArray devices = root["vrdevices"].to<JsonArray>();

  for (int i = 0; i < virtualRemotes.getMaxRemotes(); i++)
  {
    if (virtualRemotes.isEmptySlot(i))
      continue;
    JsonObject device = devices.add<JsonObject>();
    device["idx"] = i;
    device["name"] = virtualRemotes.getRemoteNamebyIndex(i);
    uint16_t remType = static_cast<uint16_t>(virtualRemotes.getRemoteType(i));
    device["type"] = remType;
    device["presets"] = HADiscConfig::getPresetsForType(remType);
  }
}

void getIthoSettingsBackupJSON(JsonObject root)
{

  if (ithoSettingsArray != nullptr)
  {
    for (uint16_t i = 0; i < currentIthoSettingsLength(); i++)
    {
      char buf[12];
      itoa(i, buf, 10);

      if (ithoSettingsArray[i].type == ithoSettings::is_int && ithoSettingsArray[i].length == 1 && ithoSettingsArray[i].is_signed)
      {
        int8_t val;
        std::memcpy(&val, &ithoSettingsArray[i].value, sizeof(val));
        root[buf] = val;
      }
      else if (ithoSettingsArray[i].type == ithoSettings::is_int && ithoSettingsArray[i].length == 2 && ithoSettingsArray[i].is_signed)
      {
        int16_t val;
        std::memcpy(&val, &ithoSettingsArray[i].value, sizeof(val));
        root[buf] = val;
      }
      else if (ithoSettingsArray[i].type == ithoSettings::is_int && ithoSettingsArray[i].length == 4 && ithoSettingsArray[i].is_signed)
      {
        root[buf] = ithoSettingsArray[i].value;
      }
      else
      {
        uint32_t val;
        std::memcpy(&val, &ithoSettingsArray[i].value, sizeof(val));
        root[buf] = val;
      }
    }
  }
}

bool ithoExecCommand(const char *command, cmdOrigin origin)
{
  if (systemConfig.itho_vremoteapi)
  {
    D_LOG("SYS: exec i2c cmd:%s", command);
    ithoI2CCommand(0, command, origin);
  }
  else
  {
    D_LOG("SYS: exec non-i2c cmd:%s", command);
    if (strcmp(command, "away") == 0)
    {
      ithoSetSpeed(systemConfig.itho_low, origin);
    }
    else if (strcmp(command, "low") == 0)
    {
      ithoSetSpeed(systemConfig.itho_low, origin);
    }
    else if (strcmp(command, "medium") == 0)
    {
      ithoSetSpeed(systemConfig.itho_medium, origin);
    }
    else if (strcmp(command, "high") == 0)
    {
      ithoSetSpeed(systemConfig.itho_high, origin);
    }
    else if (strcmp(command, "timer1") == 0)
    {
      ithoSetTimer(systemConfig.itho_timer1, origin);
    }
    else if (strcmp(command, "timer2") == 0)
    {
      ithoSetTimer(systemConfig.itho_timer2, origin);
    }
    else if (strcmp(command, "timer3") == 0)
    {
      ithoSetTimer(systemConfig.itho_timer3, origin);
    }
    else if (strcmp(command, "cook30") == 0)
    {
      ithoSetTimer(30, origin);
    }
    else if (strcmp(command, "cook60") == 0)
    {
      ithoSetTimer(60, origin);
    }
    else if (strcmp(command, "auto") == 0)
    {
      ithoSetSpeed(systemConfig.itho_medium, origin);
    }
    else if (strcmp(command, "autonight") == 0)
    {
      ithoSetSpeed(systemConfig.itho_medium, origin);
    }
    else if (strcmp(command, "clearqueue") == 0)
    {
      clearQueue = true;
    }
    else
    {
      return false;
    }
  }

  // snprintf(modestate, sizeof(modestate), "%s", command);
  // updateMQTTmodeStatus = true;

  updateMQTTihtoStatus = true;
  return true;
}

bool ithoExecRFCommand(uint8_t remote_index, const char *command, cmdOrigin origin)
{
  bool res = true;

  D_LOG("SYS: exec rf cmd:%s, idx: %d", command, remote_index);
  bool bidirectional = rfManager.radio.getRFDeviceBidirectional(remote_index);
  // Set per-remote TX power level
  bool isSendRemote = (remotes.getRemoteFunction(remote_index) == RemoteFunctions::SEND);
  rfManager.radio.setTxPowerLevel(remotes.getRemoteTxPower(remote_index));
  if (bidirectional)
    rfManager.radio.setSendTries(1);
  disableRF_ISR();

  if (strcmp(command, "away") == 0)
  {
    rfManager.radio.sendRFCommand(remote_index, IthoCommand::IthoAway);
  }
  else if (strcmp(command, "low") == 0)
  {
    rfManager.radio.sendRFCommand(remote_index, IthoCommand::IthoLow);
  }
  else if (strcmp(command, "medium") == 0)
  {
    rfManager.radio.sendRFCommand(remote_index, IthoCommand::IthoMedium);
  }
  else if (strcmp(command, "high") == 0)
  {
    rfManager.radio.sendRFCommand(remote_index, IthoCommand::IthoHigh);
  }
  else if (strcmp(command, "timer1") == 0)
  {
    rfManager.radio.sendRFCommand(remote_index, IthoCommand::IthoTimer1);
  }
  else if (strcmp(command, "timer2") == 0)
  {
    rfManager.radio.sendRFCommand(remote_index, IthoCommand::IthoTimer2);
  }
  else if (strcmp(command, "timer3") == 0)
  {
    rfManager.radio.sendRFCommand(remote_index, IthoCommand::IthoTimer3);
  }
  else if (strcmp(command, "cook30") == 0)
  {
    rfManager.radio.sendRFCommand(remote_index, IthoCommand::IthoCook30);
  }
  else if (strcmp(command, "cook60") == 0)
  {
    rfManager.radio.sendRFCommand(remote_index, IthoCommand::IthoCook60);
  }
  else if (strcmp(command, "auto") == 0)
  {
    rfManager.radio.sendRFCommand(remote_index, IthoCommand::IthoAuto);
  }
  else if (strcmp(command, "autonight") == 0)
  {
    rfManager.radio.sendRFCommand(remote_index, IthoCommand::IthoAutoNight);
  }
  else if (strcmp(command, "join") == 0)
  {
    rfManager.radio.setBindInitiatorActive(true, remote_index);
    startBindInitiatorTimeout();
    rfManager.radio.setSendTries(1);
    rfManager.radio.sendRFCommand(remote_index, IthoCommand::IthoJoin);
    rfManager.radio.setSendTries(3);
  }
  else if (strcmp(command, "leave") == 0)
  {
    rfManager.radio.sendRFCommand(remote_index, IthoCommand::IthoLeave);
  }
  else if (strcmp(command, "motion_on") == 0)
  {
    rfManager.radio.send2E10(remote_index, IthoCommand::IthoPIRmotionOn);
  }
  else if (strcmp(command, "motion_off") == 0)
  {
    rfManager.radio.send2E10(remote_index, IthoCommand::IthoPIRmotionOff);
  }
  else
  {
    res = false;
  }

  char buf[32]{};
  snprintf(buf, sizeof(buf), "rfremotecmd:%s, idx:%d", (res ? command : "unknown"), remote_index);
  logLastCommand(buf, origin);

  // Track last command per remote so external integrations (HA) can show
  // per-remote state. Only meaningful for SEND remotes — RX remotes get
  // their own lastcmd via addCapabilities() from received RF messages.
  if (res && isSendRemote)
    remotes.setLastCmd(remote_index, command);

  enableRF_ISR();
  rfManager.radio.setTxPowerLevel(0xC0); // restore default power
  if (bidirectional)
    rfManager.radio.setSendTries(3);
  return res;
}

bool ithoSendRFCO2(uint8_t remote_index, uint16_t co2level, cmdOrigin origin)
{
  if (remote_index >= remotes.getMaxRemotes())
    return false;

  if (remotes.getRemoteType(remote_index) != RemoteTypes::RFTCO2)
  {
    E_LOG("SYS: rfco2 failed - remote %d is not RFT CO2 type", remote_index);
    return false;
  }

  D_LOG("SYS: send rfco2:%d, idx:%d", co2level, remote_index);

  rfManager.radio.setTxPowerLevel(remotes.getRemoteTxPower(remote_index));
  bool bidirectional = rfManager.radio.getRFDeviceBidirectional(remote_index);
  if (bidirectional)
    rfManager.radio.setSendTries(1);

  disableRF_ISR();
  rfManager.radio.send1298(remote_index, co2level);
  enableRF_ISR();

  rfManager.radio.setTxPowerLevel(0xC0);
  if (bidirectional)
    rfManager.radio.setSendTries(3);

  char buf[32]{};
  snprintf(buf, sizeof(buf), "rfco2:%d, idx:%d", co2level, remote_index);
  logLastCommand(buf, origin);

  return true;
}

bool ithoSendRFDemand(uint8_t remote_index, uint8_t demand, uint8_t zone, cmdOrigin origin)
{
  if (remote_index >= remotes.getMaxRemotes())
    return false;

  RemoteTypes rtype = remotes.getRemoteType(remote_index);
  if (rtype != RemoteTypes::RFTCO2 && rtype != RemoteTypes::RFTRV)
  {
    E_LOG("SYS: rfdemand failed - remote %d is not RFT CO2 or RFT RV type", remote_index);
    return false;
  }

  if (demand > 200)
    demand = 200;

  D_LOG("SYS: send rfdemand:%d, zone:%d, idx:%d", demand, zone, remote_index);

  rfManager.radio.setTxPowerLevel(remotes.getRemoteTxPower(remote_index));
  bool bidirectional = rfManager.radio.getRFDeviceBidirectional(remote_index);
  if (bidirectional)
    rfManager.radio.setSendTries(1);

  disableRF_ISR();
  rfManager.radio.send31E0(remote_index, zone, demand, 0x00);
  enableRF_ISR();

  ithoFanDemand = demand;

  rfManager.radio.setTxPowerLevel(0xC0);
  if (bidirectional)
    rfManager.radio.setSendTries(3);

  char buf[40]{};
  snprintf(buf, sizeof(buf), "rfdemand:%d, zone:%d, idx:%d", demand, zone, remote_index);
  logLastCommand(buf, origin);

  return true;
}

int findFirstBidirectionalSendRemote()
{
  for (int i = 0; i < remotes.getMaxRemotes(); i++)
  {
    if (remotes.isEmptySlot(i))
      continue;
    if (remotes.getRemoteFunction(i) != RemoteFunctions::SEND)
      continue;
    if (!rfManager.radio.getRFDeviceBidirectional(i))
      continue;
    return i;
  }
  return -1;
}

// Single shared implementation behind the three public wrappers below.
// send31DA / send31D9 bits select which opcode(s) actually go out; the
// destOverride snapshot-and-restore dance happens once around the
// whole burst so both halves of a paired call share one destination.
static void sendRFStatusRequestInternal(uint8_t remote_index, bool send31DA, bool send31D9, const uint8_t *destOverride)
{
  if (remote_index >= remotes.getMaxRemotes())
    return;
  if (!send31DA && !send31D9)
    return;

  // Match the TX-power / send-tries / ISR pattern used by the other RF
  // send paths in this file (see ithoSendRFDemand at line ~695).
  rfManager.radio.setTxPowerLevel(remotes.getRemoteTxPower(remote_index));
  rfManager.radio.setSendTries(1);

  // Optional one-shot destinationID override. Snapshot the slot's
  // current destinationID via the CC1101 layer's read-only accessor,
  // swap in the override, send, then restore. Lets the debug page
  // probe a specific Itho address without modifying the saved config.
  uint8_t savedDest[3] = {0, 0, 0};
  bool restoreDest = false;
  if (destOverride != nullptr)
  {
    const auto &devs = rfManager.radio.getRFdevices();
    savedDest[0] = devs.device[remote_index].destinationID[0];
    savedDest[1] = devs.device[remote_index].destinationID[1];
    savedDest[2] = devs.device[remote_index].destinationID[2];
    rfManager.radio.updateDestinationID(destOverride[0], destOverride[1], destOverride[2], remote_index);
    restoreDest = true;
  }

  // Each frame gets its own ISR-disabled critical section, mirroring the
  // single-opcode pattern in task_cc1101.cpp's send31DA/send31D9 blocks.
  // Stuffing both sends into one block was leaving the CC1101 in an
  // intermediate state for the second TX — first opcode went out, second
  // silently didn't. The brief delay between them gives the radio time to
  // cycle through RX → IDLE → TX again.
  if (send31DA)
  {
    disableRF_ISR();
    rfManager.radio.sendRQ31DA(remote_index);
    enableRF_ISR();
  }
  if (send31DA && send31D9)
    delay(50);
  if (send31D9)
  {
    disableRF_ISR();
    rfManager.radio.sendRQ31D9(remote_index);
    enableRF_ISR();
  }

  if (restoreDest)
  {
    rfManager.radio.updateDestinationID(savedDest[0], savedDest[1], savedDest[2], remote_index);
  }

  rfManager.radio.setTxPowerLevel(0xC0);
  rfManager.radio.setSendTries(3);

  // Read back the destination that was actually used so the log line
  // is unambiguous regardless of whether an override was supplied.
  const auto &devs = rfManager.radio.getRFdevices();
  uint8_t actualDest[3] = {
      devs.device[remote_index].destinationID[0],
      devs.device[remote_index].destinationID[1],
      devs.device[remote_index].destinationID[2]};
  const char *what = (send31DA && send31D9) ? "31DA+31D9"
                                            : (send31DA ? "31DA" : "31D9");
  I_LOG("SYS: sent RF %s status request via remote idx:%d, dest:%02X,%02X,%02X",
        what, remote_index, actualDest[0], actualDest[1], actualDest[2]);
}

void sendRFStatusRequest(uint8_t remote_index, const uint8_t *destOverride)
{
  sendRFStatusRequestInternal(remote_index, true, true, destOverride);
}

void sendRF31DARequest(uint8_t remote_index, const uint8_t *destOverride)
{
  sendRFStatusRequestInternal(remote_index, true, false, destOverride);
}

void sendRF31D9Request(uint8_t remote_index, const uint8_t *destOverride)
{
  sendRFStatusRequestInternal(remote_index, false, true, destOverride);
}

bool ithoSetSpeed(const char *speed, cmdOrigin origin)
{
  D_LOG("SYS: ithoSetSpeed: char speed:%s", speed);
  uint16_t val = strtoul(speed, NULL, 10);
  return ithoSetSpeed(val, origin);
}

bool ithoSetSpeed(uint16_t speed, cmdOrigin origin)
{
  if (speed < 256)
  {
    D_LOG("PWM: set speed:%d", speed);
    nextIthoVal = speed;
    nextIthoTimer = 0;
    updateItho();
  }
  else
  {
    D_LOG("PWM: set speed: value out of range");
    return false;
  }

  char buf[32]{};
  snprintf(buf, sizeof(buf), "speed:%d", speed);
  logLastCommand(buf, origin);
  return true;
}

bool ithoSetTimer(const char *timer, cmdOrigin origin)
{
  uint16_t t = strtoul(timer, NULL, 10);
  return ithoSetTimer(t, origin);
}

bool ithoSetTimer(uint16_t timer, cmdOrigin origin)
{
  D_LOG("PWM: set timer:%dmin", timer);
  if (timer > 0 && timer < 65535)
  {
    nextIthoTimer = timer;
    nextIthoVal = systemConfig.itho_high;
    updateItho();
  }
  else
  {
    return false;
  }

  char buf[32]{};
  snprintf(buf, sizeof(buf), "timer:%d", timer);
  logLastCommand(buf, origin);
  return true;
}

bool ithoSetSpeedTimer(const char *speed, const char *timer, cmdOrigin origin)
{
  uint16_t speedval = strtoul(speed, NULL, 10);
  uint16_t timerval = strtoul(timer, NULL, 10);
  return ithoSetSpeedTimer(speedval, timerval, origin);
}

bool ithoSetSpeedTimer(uint16_t speed, uint16_t timer, cmdOrigin origin)
{
  D_LOG("PWM: set speed and timer");
  if (speed < 255)
  {
    nextIthoVal = speed;
    nextIthoTimer = timer;
    updateItho();
  }
  else
  {
    return false;
  }

  char buf[32]{};
  snprintf(buf, sizeof(buf), "speed:%d,timer:%d", speed, timer);
  logLastCommand(buf, origin);
  return true;
}

void logLastCommand(const char *command, cmdOrigin origin)
{

  if (origin != REMOTE)
  {
    const char *source;
    auto it = cmdOriginMap.find(origin);
    if (it != cmdOriginMap.end())
      source = it->second;
    else
      source = cmdOriginMap.rbegin()->second;
    logLastCommand(command, source);
  }
  else
  {
    logLastCommand(command, remotes.lastRemoteName);
  }
}

void logLastCommand(const char *command, const char *source)
{

  strlcpy(lastCmd.source, source, sizeof(lastCmd.source));
  strlcpy(lastCmd.command, command, sizeof(lastCmd.command));

  if (time(nullptr))
  {
    time_t now;
    time(&now);
    lastCmd.timestamp = now;
  }
  else
  {
    lastCmd.timestamp = (time_t)millis();
  }
}

void getLastCMDinfoJSON(JsonObject root)
{

  root["source"] = lastCmd.source;
  root["command"] = lastCmd.command;
  root["timestamp"] = lastCmd.timestamp;
}

void updateItho()
{
  if (systemConfig.itho_rf_support)
  {
    IthoCMD.once_ms(150, addToQueue);
  }
  else
  {
    addToQueue();
  }
}

void addToQueue()
{
  ithoQueue.addToQueue(nextIthoVal, nextIthoTimer, systemConfig.nonQ_cmd_clearsQ);
}

void setRFdebugLevel(uint8_t level)
{
  rfManager.radio.setAllowAll(true);
  if (level == 2)
  {
    rfManager.radio.setAllowAll(false);
  }
  I_LOG("SYS: RF debug level = %d", level);
}

double round(float value, int precision)
{
  double pow10 = pow(10.0, precision);
  return static_cast<int>(value * pow10 + 0.5) / pow10;
}

char toHex(uint8_t c)
{
  return c < 10 ? c + '0' : c + 'A' - 10;
}

// Function to convert a hex string to an integer
int hexStringToInt(const std::string &hexStr) // throw(std::invalid_argument)
{
  int result = 0;
  for (char c : hexStr)
  {
    result *= 16;
    if (c >= '0' && c <= '9')
    {
      result += (c - '0');
    }
    else if (c >= 'A' && c <= 'F')
    {
      result += (c - 'A' + 10);
    }
    else if (c >= 'a' && c <= 'f')
    {
      result += (c - 'a' + 10);
    }
    // else
    // {
    //   throw std::invalid_argument("Invalid character in hex string: " + hexStr);
    // }
  }
  return result;
}

// Function to parse the comma-separated hex string ie "3A,D1,F1"
std::vector<int> parseHexString(const std::string &input) // throw(std::invalid_argument)
{
  std::vector<int> result;
  size_t start = 0;
  size_t end = input.find(',');

  while (end != std::string::npos)
  {
    std::string hexStr = input.substr(start, end - start);

    // Convert hex string to integer and add to the result vector
    result.push_back(hexStringToInt(hexStr));

    start = end + 1;
    end = input.find(',', start);
  }

  // Add the last hex value
  std::string hexStr = input.substr(start);
  result.push_back(hexStringToInt(hexStr));

  return result;
}

bool isNumeric(const std::string &str)
{
  return std::all_of(str.begin(), str.end(), ::isdigit);
}

// Parses a version string into numeric and optional pre-release components
// Returns false if parsing fails due to invalid format
bool parseVersion(const std::string &version, std::vector<int> &numbers, std::string &prerelease)
{
  size_t pos = 0, found;
  size_t hyphen = version.find('-');
  std::string numericPart = (hyphen != std::string::npos) ? version.substr(0, hyphen) : version;
  prerelease = (hyphen != std::string::npos) ? version.substr(hyphen + 1) : "";

  while ((found = numericPart.find('.', pos)) != std::string::npos)
  {
    std::string segment = numericPart.substr(pos, found - pos);
    if (!segment.empty() && isNumeric(segment))
    {
      numbers.push_back(stoi(segment));
    }
    else
    {
      return false; // Invalid numeric segment
    }
    pos = found + 1;
  }

  if (pos < numericPart.length())
  {
    std::string lastSegment = numericPart.substr(pos);
    if (!lastSegment.empty() && isNumeric(lastSegment))
    {
      numbers.push_back(stoi(lastSegment));
    }
    else
    {
      return false; // Invalid last segment
    }
  }

  return true; // Successfully parsed
}

int compareVersions(const std::string &v1, const std::string &v2)
{
  std::vector<int> nums1, nums2;
  std::string pre1, pre2;

  if (!parseVersion(v1, nums1, pre1) || !parseVersion(v2, nums2, pre2))
  {
    return -99; // Return error code for invalid input format
  }

  for (int i = 0; i < std::max(nums1.size(), nums2.size()); ++i)
  {
    int num1 = i < nums1.size() ? nums1[i] : 0;
    int num2 = i < nums2.size() ? nums2[i] : 0;

    if (num1 > num2)
      return 1;
    if (num1 < num2)
      return -1;
  }

  if (pre1.empty() && !pre2.empty())
    return 1; // No pre-release is higher than any pre-release
  if (!pre1.empty() && pre2.empty())
    return -1;
  if (pre1.empty() && pre2.empty())
    return 0;

  return pre1.compare(pre2); // Compare pre-releases if both are not empty
}

void checkFirmwareUpdate()
{
  WiFiClientSecure *secclient = new WiFiClientSecure;
  if (!secclient)
  {
    E_LOG("SYS: firmware check - failed to allocate WiFiClientSecure");
    return;
  }
  secclient->setInsecure(); // set secure client without certificate

  HTTPClient https;

  if (!https.begin(*secclient, "https://raw.githubusercontent.com/arjenhiemstra/ithowifi/master/compiled_firmware_files/firmware.json"))
  {
    E_LOG("SYS: firmware check - https.begin() failed");
    delete secclient;
    return;
  }

  int httpCode = https.GET();
  if (httpCode <= 0)
  {
    E_LOG("SYS: firmware check - GET failed: %s", https.errorToString(httpCode).c_str());
    https.end();
    delete secclient;
    return;
  }
  if (httpCode != HTTP_CODE_OK)
  {
    E_LOG("SYS: firmware check - HTTP %d", httpCode);
    https.end();
    delete secclient;
    return;
  }
  if (https.getSize() >= MAX_FIRMWARE_HTTPS_RESPONSE_SIZE)
  {
    E_LOG("SYS: firmware check - response too large: %d", https.getSize());
    https.end();
    delete secclient;
    return;
  }

  String payloadString = https.getString().c_str();
  const char *payload = payloadString.c_str();

  JsonDocument root;
  DeserializationError error = deserializeJson(root, payload);
  if (error)
  {
    E_LOG("SYS: firmware check - JSON parse error: %s", error.c_str());
    https.end();
    delete secclient;
    return;
  }

  JsonVariant hwNode = root["hw_rev"][hardwareManager.hw_revision];
  if (hwNode.isNull())
  {
    E_LOG("SYS: firmware check - no entry for hw_rev %d in firmware.json", hardwareManager.hw_revision);
    https.end();
    delete secclient;
    return;
  }

  firmwareInfo.fw_update_available = compareVersions(hwNode["latest_fw"] | "error", fw_version);

  strlcpy(firmwareInfo.latest_fw, hwNode["latest_fw"] | "error", sizeof(firmwareInfo.latest_fw));
  strlcpy(firmwareInfo.latest_beta_fw, hwNode["latest_beta_fw"] | "error", sizeof(firmwareInfo.latest_beta_fw));
  strlcpy(firmwareInfo.link, hwNode["link"] | "", sizeof(firmwareInfo.link));
  strlcpy(firmwareInfo.link_beta, hwNode["link_beta"] | "", sizeof(firmwareInfo.link_beta));
  D_LOG("SYS: latest_fw:%s, latest_beta:%s", firmwareInfo.latest_fw, firmwareInfo.latest_beta_fw);
  D_LOG("SYS: fw_update_available:%d", firmwareInfo.fw_update_available);
  // 1: newer version available online, 0: no new version available, -1: current version is newer than online version, -99: compare unsuccessful

  https.end();
  delete secclient;
}

volatile int otaUpdateProgress = -1; // -1=idle, 0-100=progress, 101=done, -2=error
volatile bool otaUpdateRequested = false;
volatile bool otaUpdateBeta = false;
char otaUpdateURL[160] = {};

void triggerOTAUpdate(bool beta)
{
  otaUpdateURL[0] = '\0';
  otaUpdateBeta = beta;
  otaUpdateRequested = true;
}

void triggerOTAUpdateFromURL(const char *url)
{
  strlcpy(otaUpdateURL, url, sizeof(otaUpdateURL));
  otaUpdateRequested = true;
}

bool performOTAUpdate(bool beta)
{
  const char *url = beta ? firmwareInfo.link_beta : firmwareInfo.link;
  return performOTAUpdateFromURL(url);
}

bool performOTAUpdateFromURL(const char *url)
{
  if (url == nullptr || strlen(url) == 0)
  {
    E_LOG("OTA: no firmware URL available");
    return false;
  }

  I_LOG("OTA: starting update from %s", url);
  logMessagejson("Firmware update starting...", WEBINTERFACE);

  WiFiClientSecure secclient;
  secclient.setInsecure();

  httpUpdate.setFollowRedirects(HTTPC_FORCE_FOLLOW_REDIRECTS);
  httpUpdate.rebootOnUpdate(false);

  otaUpdateProgress = 0;

  httpUpdate.onProgress([](int cur, int total)
                        {
    if (total > 0)
      otaUpdateProgress = (cur * 100) / total; });

  t_httpUpdate_return ret = httpUpdate.update(secclient, url);

  switch (ret)
  {
  case HTTP_UPDATE_FAILED:
    otaUpdateProgress = -2;
    E_LOG("OTA: update failed: %s", httpUpdate.getLastErrorString().c_str());
    logMessagejson("Firmware update failed!", WEBINTERFACE);
    return false;

  case HTTP_UPDATE_NO_UPDATES:
    otaUpdateProgress = -1;
    I_LOG("OTA: no update available");
    return false;

  case HTTP_UPDATE_OK:
    otaUpdateProgress = 101;
    I_LOG("OTA: update successful, rebooting...");
    logMessagejson("Firmware update successful, rebooting...", WEBINTERFACE);
    delay(1000);
    shouldReboot = true;
    return true;
  }
  return false;
}
