arjenhiemstra/ithowifi/software/NRG_itho_wifi/main/websocket.cpp

#include "websocket.h"
#include "managers/SecureWebCommLite.h"

static std::unordered_map<uint32_t, std::string> g_wsBuffers;
static SemaphoreHandle_t g_wsBuffersMutex = xSemaphoreCreateMutex();
// rfSelectedSourceForParsing is defined in IthoStatus.cpp
AsyncWebServer wsserver(8000);
WebSerial *webSerial = nullptr;

void onWsEvent(AsyncWebSocket *server, AsyncWebSocketClient *client, AwsEventType type, void *arg, uint8_t *data, size_t len);

void websocketInit()
{
  // Initialize lightweight secure communication
  if (!secureWebCommLite.init())
  {
    W_LOG("WEB: Secure communication init failed");
  }

  // attach AsyncWebSocket
  ws.onEvent(onWsEvent);
  wsserver.addHandler(&ws);
  wsserver.begin();

  // if enable a web based serial terminal will be available at http://IP:8000/webserial
  if (logConfig.webserial_active)
  {
    webSerial = new WebSerial();
    webSerial->onMessage([](const std::string &msg)
                         { Serial.println(msg.c_str()); });
    if (systemConfig.syssec_web)
    {
      webSerial->setAuthentication(systemConfig.sys_username, systemConfig.sys_password);
    }
    webSerial->begin(&wsserver);
  }
}

void jsonWsSend(const char *rootName)
{
  JsonDocument root;

  if (strcmp(rootName, "wifisettings") == 0)
  {
    JsonObject nested = root[rootName].to<JsonObject>();
    wifiConfig.get(nested);
    // Mask passwords before sending to web UI
    nested["passwd"] = strlen(wifiConfig.passwd) > 0 ? "********" : "";
    nested["appasswd"] = strlen(wifiConfig.appasswd) > 0 ? "********" : "";
    if (strcmp(wifiConfig.dhcp, "on") == 0)
    {
      nested["ip"] = WiFi.localIP().toString();
      nested["subnet"] = WiFi.subnetMask().toString();
      nested["gateway"] = WiFi.gatewayIP().toString();
      nested["dns1"] = WiFi.dnsIP().toString();
      nested["dns2"] = WiFi.dnsIP(1).toString();
    }
    if (strcmp(wifiConfig.hostname, "") == 0) // defualt config still there
    {
      nested["hostname"] = hostName();
    }
  }
  else if (strcmp(rootName, "wifistat") == 0)
  {

    JsonObject wifiinfo = root[rootName].to<JsonObject>();
    IPAddress ip = WiFi.localIP();
    char wifiip[16] = {};
    snprintf(wifiip, sizeof(wifiip), "%d.%d.%d.%d", ip[0], ip[1], ip[2], ip[3]);

    char apremain[16] = {};
    long timeout = wifiConfig.aptimeout * 60 * 1000;
    long time = (millis() - APmodeTimeout) < timeout ? (timeout - (millis() - APmodeTimeout)) / 1000 : 0;

    if (!wifiModeAP || wifiConfig.aptimeout == 0)
    {
      snprintf(apremain, sizeof(apremain), "%s", "off");
    }
    else if (wifiConfig.aptimeout == 255)
    {
      snprintf(apremain, sizeof(apremain), "%s", "always on");
    }
    else
    {
      snprintf(apremain, sizeof(apremain), "%ld sec.", time);
    }

    char apssid[32]{};

    snprintf(apssid, sizeof(apssid), "%s%02x%02x", espName, sys.getMac(4), sys.getMac(5));

    wifiinfo["wifissid"] = WiFi.SSID();
    wifiinfo["wifimac"] = WiFi.macAddress();
    wifiinfo["wificonnstat"] = wifiConfig.wl_status_to_name(WiFi.status());
    wifiinfo["wifiip"] = wifiip;
    wifiinfo["apactive"] = wifiModeAP ? "yes" : "no";
    wifiinfo["apremain"] = apremain;
    wifiinfo["apssid"] = apssid;
    wifiinfo["apip"] = "192.168.4.1";
  }
  else if (strcmp(rootName, "systemsettings") == 0)
  {
    JsonObject nested = root[rootName].to<JsonObject>();
    systemConfig.get(nested);
    // Mask passwords before sending to web UI
    nested["sys_password"] = strlen(systemConfig.sys_password) > 0 ? "********" : "";
    nested["mqtt_password"] = strlen(systemConfig.mqtt_password) > 0 ? "********" : "";
  }
  else if (strcmp(rootName, "logsettings") == 0)
  {
    JsonObject nested = root[rootName].to<JsonObject>();
    logConfig.get(nested);
    if (prevlogAvailable())
    {
      nested["prevlog"] = "/prevlog";
    }
  }
  else if (strcmp(rootName, "ithodevinfo") == 0)
  {
    JsonObject nested = root[rootName].to<JsonObject>();
    nested["itho_devtype"] = getIthoType();
    nested["itho_mfr"] = currentIthoDeviceGroup();
    nested["itho_hwversion"] = currentItho_hwversion();
    nested["itho_fwversion"] = currentItho_fwversion();
    nested["itho_setlen"] = currentIthoSettingsLength();
  }
  else if (strcmp(rootName, "ithostatusinfo") == 0)
  {
    JsonObject nested = root[rootName].to<JsonObject>();
    uint8_t count = getIthoStatusJSON(nested);
    root["count"] = count;
  }
  else if (strcmp(rootName, "hadiscinfo") == 0)
  {
    JsonObject nested = root["ithostatusinfo"].to<JsonObject>();
    uint8_t count = getIthoStatusJSON(nested);
    root["count"] = count;
    root["target"] = "hadisc";
    root["itho_status_ready"] = ithoStatusReady();
    root["iis"] = itho_init_status;
    // Include RF and virtual remote device info for HA discovery
    getRFDevicesForHADiscJSON(root.as<JsonObject>());
    getVirtualRemotesForHADiscJSON(root.as<JsonObject>());
  }
  else if (strcmp(rootName, "hadiscsettings") == 0)
  {
    JsonObject nested = root[rootName].to<JsonObject>();
    haDiscConfig.get(nested);
  }
  else if (strcmp(rootName, "debuginfo") == 0)
  {
    JsonObject nested = root[rootName].to<JsonObject>();
    nested["configversion"] = CONFIG_VERSION;
    nested["bfree"] = ACTIVE_FS.usedBytes();
    nested["btotal"] = ACTIVE_FS.totalBytes();
    nested["bfree"] = ACTIVE_FS.usedBytes();
    nested["cc1101taskmem"] = TaskCC1101HWmark;
    nested["mqtttaskmem"] = TaskMQTTHWmark;
    nested["webtaskmem"] = TaskWebHWmark;
    nested["cltaskmem"] = TaskConfigAndLogHWmark;
    nested["syscontaskmem"] = TaskSysControlHWmark;
    TaskHandle_t loopTaskHandle = xTaskGetHandle("loopTask");
    if (loopTaskHandle != NULL)
    {
      nested["looptaskmem"] = static_cast<uint32_t>(uxTaskGetStackHighWaterMark(loopTaskHandle));
    }
  }
  else if (strcmp(rootName, "i2cdebuglog") == 0) // i2cdebuglog
  {
    i2cLogger.get(root.to<JsonObject>(), rootName);
  }
  else if (strcmp(rootName, "remtypeconf") == 0)
  {
    JsonObject nested = root[rootName].to<JsonObject>();
    nested["remtype"] = static_cast<uint16_t>(virtualRemotes.getRemoteType(0)); // FIXME, should also support remotes on other positions than only index 0
  }
  else if (strcmp(rootName, "remotes") == 0)
  {
    JsonObject obj = root.to<JsonObject>(); // Fill the object
    remotes.get(obj, rootName);
  }
  else if (strcmp(rootName, "vremotes") == 0)
  {
    JsonObject obj = root.to<JsonObject>(); // Fill the object
    virtualRemotes.get(obj, rootName);
  }
  else if (strcmp(rootName, "rfstatusinfo") == 0)
  {
    JsonObject nested = root[rootName].to<JsonObject>();
    getRFStatusJSON(nested, rfSelectedSourceForParsing);
  }
  else if (strcmp(rootName, "rfstatusconfig") == 0)
  {
    JsonObject nested = root[rootName].to<JsonObject>();
    getRFStatusConfigJSON(nested, rfSelectedSourceForParsing);
  }
  else if (strcmp(rootName, "chkpart") == 0)
  {
    root["chkpart"] = chk_partition_res ? "partition scheme supports firmware versions from 2.4.4-beta7 and upwards" : "partion scheme supports firmware versions 2.4.4-beta6 and older";
  }
  notifyClients(root.as<JsonObject>());
}

void handle_ws_message(JsonObject root)
{
  // D_LOG("%s", msg.c_str());

  // SECURITY LAYER 2: Handle session key request
  if (root["command"].is<const char *>())
  {
    const char *cmd = root["command"];
    if (strcmp(cmd, "get_session_key") == 0)
    {
      secureWebCommLite.send_session_key_response();
      return;
    }
  }

  if (root["wifiscan"].is<bool>() && root["wifiscan"].as<bool>())
  {
    D_LOG("NET: Start wifi scan");
    runscan = true;
  }
  if (root["sysstat"].is<bool>() && root["sysstat"].as<bool>())
  {
    sysStatReq = true;
  }
  if (root["remtype"].is<bool>() && root["remtype"].as<bool>())
  {
    jsonWsSend("remtypeconf");
  }

  // ---------- "debugvalues" vs. "i2cdebuglog" ----------
  if (root["debugvalues"].is<bool>() && root["debugvalues"].as<bool>())
  {
    jsonWsSend("debuginfo");
  }
  else if (root["i2cdebuglog"].is<bool>() && root["i2cdebuglog"].as<bool>())
  {
    jsonWsSend("i2cdebuglog");
  }

  // ---------- WiFi/system/log/hadisc config ----------
  if (root["wifisettings"].is<JsonObject>())
  {
    JsonObject wifiObj = root["wifisettings"].as<JsonObject>();
    // Decrypt inline secure credentials before set() processes the fields
    if (wifiObj["secure_credentials"].is<JsonObject>())
    {
      JsonObject creds = wifiObj["secure_credentials"].as<JsonObject>();
      char decrypted[65] = {};
      if (creds["passwd"].is<JsonObject>())
      {
        const char *ct = creds["passwd"]["ct"] | "";
        const char *nonce = creds["passwd"]["nonce"] | "";
        if (secureWebCommLite.decryptField(ct, nonce, decrypted, sizeof(decrypted)))
        {
          wifiObj["passwd"] = decrypted;
        }
      }
      if (creds["appasswd"].is<JsonObject>())
      {
        const char *ct = creds["appasswd"]["ct"] | "";
        const char *nonce = creds["appasswd"]["nonce"] | "";
        if (secureWebCommLite.decryptField(ct, nonce, decrypted, sizeof(decrypted)))
        {
          wifiObj["appasswd"] = decrypted;
        }
      }
      mbedtls_platform_zeroize(decrypted, sizeof(decrypted));
      wifiObj.remove("secure_credentials");
    }
    if (wifiConfig.set(wifiObj))
    {
      saveWifiConfigflag = true;
    }
  }
  if (root["systemsettings"].is<JsonObject>())
  {
    JsonObject sysObj = root["systemsettings"].as<JsonObject>();
    // Decrypt inline secure credentials before set() processes the fields
    if (sysObj["secure_credentials"].is<JsonObject>())
    {
      JsonObject creds = sysObj["secure_credentials"].as<JsonObject>();
      char decrypted[65] = {};
      if (creds["sys_password"].is<JsonObject>())
      {
        const char *ct = creds["sys_password"]["ct"] | "";
        const char *nonce = creds["sys_password"]["nonce"] | "";
        if (secureWebCommLite.decryptField(ct, nonce, decrypted, sizeof(decrypted)))
        {
          sysObj["sys_password"] = decrypted;
        }
      }
      if (creds["mqtt_password"].is<JsonObject>())
      {
        const char *ct = creds["mqtt_password"]["ct"] | "";
        const char *nonce = creds["mqtt_password"]["nonce"] | "";
        if (secureWebCommLite.decryptField(ct, nonce, decrypted, sizeof(decrypted)))
        {
          sysObj["mqtt_password"] = decrypted;
        }
      }
      mbedtls_platform_zeroize(decrypted, sizeof(decrypted));
      sysObj.remove("secure_credentials");
    }
    if (systemConfig.set(sysObj))
    {
      saveSystemConfigflag = true;
      remotes.setMaxRemotes(systemConfig.itho_numrfrem);
      virtualRemotes.setMaxRemotes(systemConfig.itho_numvrem);

      // Apply itho_pwm2i2c: send I2C init command on CVE devices when enabled
      if (systemConfig.itho_pwm2i2c == 1 &&
          (hardwareManager.hardware_rev_det == 0x3F || hardwareManager.hardware_rev_det == 0x03))
      {
        N_LOG("I2C: sendI2CPWMinit triggered by settings save");
        sendI2CPWMinit();
      }

      // Apply i2c_safe_guard and i2c_sniffer: update runtime state
      if (hardwareManager.i2c_sniffer_capable)
      {
        auto *sg = static_cast<i2c_safe_guard_t *>(i2cManager.safe_guard);
        sg->i2c_safe_guard_enabled = (systemConfig.i2c_safe_guard > 0 &&
                                       currentIthoDeviceID() == 0x1B &&
                                       systemConfig.syssht30 == 0 &&
                                       currentItho_fwversion() >= 25);
        sg->sniffer_enabled = (systemConfig.i2c_sniffer == 1);
        if (sg->i2c_safe_guard_enabled || sg->sniffer_enabled)
          i2cSnifferEnable();
        else if (!sg->sniffer_web_enabled)
          i2cSnifferDisable();
      }

      // Apply fw_check: trigger firmware update check soon when enabled
      if (systemConfig.fw_check)
        getFWupdateInfo = millis() - 24UL * 60 * 60 * 1000 - 1;
    }
  }
  if (root["logsettings"].is<JsonObject>())
  {
    if (logConfig.set(root["logsettings"].as<JsonObject>()))
    {
      saveLogConfigflag = true;
    }
    setRFdebugLevel(logConfig.rfloglevel);
  }
  if (root["hadiscsettings"].is<JsonObject>())
  {
    if (haDiscConfig.set(root["hadiscsettings"].as<JsonObject>()))
    {
      saveHADiscConfigflag = true;
    }
    else
    {
      E_LOG("SYS: error - hadiscsettings: set config failed");
    }
  }

  // ---------- "button" (string) ----------
  if (root["button"].is<const char *>())
  {
    const char *btn = root["button"].as<const char *>();
    if (strcmp(btn, "restorepart") == 0)
    {
      repartitionDevice("legacy");
    }
    else if (strcmp(btn, "checkpart") == 0)
    {
      chkpartition = true;
    }
    else if (strcmp(btn, "i2cdebugon") == 0)
    {
      systemConfig.i2cmenu = 1;
      saveSystemConfigflag = true;
    }
    else if (strcmp(btn, "i2cdebugoff") == 0)
    {
      systemConfig.i2cmenu = 0;
      saveSystemConfigflag = true;
    }
    else if (strcmp(btn, "i2csnifferon") == 0)
    {
      systemConfig.i2c_sniffer = 1;
      saveSystemConfigflag = true;
    }
    else if (strcmp(btn, "i2csnifferoff") == 0)
    {
      systemConfig.i2c_sniffer = 0;
      saveSystemConfigflag = true;
    }
  }

  // ---------- "ithobutton": can be a string or an integer ----------
  if (root["ithobutton"].is<const char *>())
  {
    i2c_result_updateweb = true;
    ithoI2CCommand(0, root["ithobutton"].as<const char *>(), WEB);
  }
  else if (root["ithobutton"].is<uint16_t>())
  {
    uint16_t val = root["ithobutton"].as<uint16_t>();
    switch (val)
    {
    case 2410:
    {
      if (root["index"].is<uint8_t>())
      {
        uint8_t idx = root["index"].as<uint8_t>();
        i2cQueueAddCmd([idx]()
                       { getSetting(idx, false, true, false); });
      }
      break;
    }
    case 24109:
    {
      if (ithoSettingsArray &&
          root["ithosetupdate"].is<uint8_t>() &&
          root["value"].is<float>())
      {
        uint8_t index = root["ithosetupdate"].as<uint8_t>();
        float fval = root["value"].as<float>();
        auto &entry = ithoSettingsArray[index];
        if (entry.type == ithoSettings::is_float)
        {
          if (entry.length == 1)
            updateSetting(index, (int8_t)(fval * entry.divider), true);
          else if (entry.length == 2)
            updateSetting(index, (int16_t)(fval * entry.divider), true);
          else if (entry.length == 4)
            updateSetting(index, (int32_t)(fval * entry.divider), true);
          else
            updateSetting(index, (int32_t)fval, true);
        }
        else
        {
          updateSetting(index, (int32_t)fval, true);
        }
      }
      break;
    }
    case 4210:
      sendQueryCounters(true);
      break;
    case 0xCE30:
      if (root["ithotemptemp"].is<int16_t>() &&
          root["ithotemp"].is<int16_t>() &&
          root["ithotimestamp"].is<uint32_t>())
      {
        setSettingCE30(root["ithotemptemp"].as<int16_t>(),
                       root["ithotemp"].as<int16_t>(),
                       root["ithotimestamp"].as<uint32_t>(),
                       true);
      }
      break;
    case 0xC000:
      if (root["itho_c000_speed1"].is<uint8_t>() &&
          root["itho_c000_speed2"].is<uint8_t>())
      {
        sendCO2speed(root["itho_c000_speed1"].as<uint8_t>(),
                     root["itho_c000_speed2"].as<uint8_t>());
      }
      break;
    case 0x9298:
      if (root["itho_9298_val"].is<uint16_t>())
      {
        sendCO2value(root["itho_9298_val"].as<uint16_t>());
      }
      break;
    case 4030:
      if (root["idx"].is<uint16_t>() &&
          root["dt"].is<uint8_t>() &&
          root["val"].is<int16_t>() &&
          root["chk"].is<uint8_t>())
      {
        setSetting4030(root["idx"].as<uint16_t>(),
                       root["dt"].as<uint8_t>(),
                       root["val"].as<int16_t>(),
                       root["chk"].as<uint8_t>(),
                       true);
      }
      break;
    }
  }

  // ---------- Quick config queries ----------
  if (root["wifisetup"].is<bool>() && root["wifisetup"].as<bool>())
  {
    jsonWsSend("wifisettings");
  }
  if (root["wifistat"].is<bool>() && root["wifistat"].as<bool>())
  {
    jsonWsSend("wifistat");
  }
  if (root["syssetup"].is<bool>() && root["syssetup"].as<bool>())
  {
    systemConfig.get_sys_settings = true;
    jsonWsSend("systemsettings");
  }
  if (root["logsetup"].is<bool>() && root["logsetup"].as<bool>())
  {
    jsonWsSend("logsettings");
  }
  if (root["mqttsetup"].is<bool>() && root["mqttsetup"].as<bool>())
  {
    systemConfig.get_mqtt_settings = true;
    jsonWsSend("systemsettings");
    sysStatReq = true;
  }
  if (root["rfsetup"].is<bool>() && root["rfsetup"].as<bool>())
  {
    systemConfig.get_rf_settings = true;
    jsonWsSend("systemsettings");
  }
  if (root["ithosetup"].is<bool>() && root["ithosetup"].as<bool>())
  {
    jsonWsSend("ithodevinfo");
    sysStatReq = true;
  }
  if (root["ithostatus"].is<bool>() && root["ithostatus"].as<bool>())
  {
    jsonWsSend("ithostatusinfo");
    sysStatReq = true;
  }
  if (root["rfstatus"].is<bool>() && root["rfstatus"].as<bool>())
  {
    rfSelectedSourceForParsing = root["source"].is<int>() ? root["source"].as<int>() : -1;
    jsonWsSend("rfstatusinfo");
  }
  if (root["rfstatusconfig"].is<bool>() && root["rfstatusconfig"].as<bool>())
  {
    rfSelectedSourceForParsing = root["source"].is<int>() ? root["source"].as<int>() : -1;
    jsonWsSend("rfstatusconfig");
  }
  if (root["rftrack"].is<JsonObject>())
  {
    JsonObject trackObj = root["rftrack"].as<JsonObject>();
    int idx = trackObj["index"].is<int>() ? trackObj["index"].as<int>() : -1;
    if (idx >= 0 && idx < MAX_RF_STATUS_SOURCES && rfStatusSources[idx].active)
    {
      if (trackObj["track"].is<bool>())
      {
        bool track = trackObj["track"].as<bool>();
        rfStatusSources[idx].tracked = track;
        if (!track)
        {
          rfStatusSources[idx].measurements31DA.clear();
          rfStatusSources[idx].measurements31D9.clear();
        }
      }
      if (trackObj["name"].is<const char *>())
        strlcpy(rfStatusSources[idx].name, trackObj["name"].as<const char *>(), sizeof(rfStatusSources[idx].name));
      saveRFTrackedConfigflag = true;
      jsonWsSend("rfstatusconfig");
    }
  }
  if (root["hadiscinfo"].is<bool>() && root["hadiscinfo"].as<bool>())
  {
    jsonWsSend("hadiscinfo");
    sysStatReq = true;
  }
  if (root["gethadiscsettings"].is<bool>() && root["gethadiscsettings"].as<bool>())
  {
    jsonWsSend("hadiscsettings");
    sysStatReq = true;
  }

  // ---------- Wizard state persistence ----------
  if (root["wizardsave"].is<int>())
  {
    int step = root["wizardsave"].as<int>();
    File f = ACTIVE_FS.open("/wizard_state", "w");
    if (f)
    {
      f.print(step);
      f.close();
    }
  }
  if (root["wizardclear"].is<bool>() && root["wizardclear"].as<bool>())
  {
    ACTIVE_FS.remove("/wizard_state");
  }

  // ---------- Itho get/refresh/update settings ----------
  if (root["ithogetsetting"].is<bool>() && root["ithogetsetting"].as<bool>())
  {
    // step1: index=0, update=false, loop=true -> reply with settings labels but null for values
    uint8_t idx = root["index"].as<uint8_t>();
    bool upd = root["update"].as<bool>();

    i2cQueueAddCmd([idx, upd]()
                   { getSetting(idx, upd, false, true); });
  }
  if (root["ithosetrefresh"].is<uint8_t>())
  {
    uint8_t idx = root["ithosetrefresh"].as<uint8_t>();
    i2cQueueAddCmd([idx]()
                   { getSetting(idx, true, false, false); });
  }
  if (root["ithosetupdate"].is<uint8_t>() && root["value"].is<float>())
  {
    if (ithoSettingsArray)
    {
      uint8_t index = root["ithosetupdate"].as<uint8_t>();
      float fval = root["value"].as<float>();
      auto &entry = ithoSettingsArray[index];
      if (entry.type == ithoSettings::is_float)
      {
        if (entry.length == 1)
          updateSetting(index, (int8_t)(fval * entry.divider), false);
        else if (entry.length == 2)
          updateSetting(index, (int16_t)(fval * entry.divider), false);
        else if (entry.length == 4)
          updateSetting(index, (int32_t)(fval * entry.divider), false);
        else
          updateSetting(index, (int32_t)fval, false);
      }
      else
      {
        updateSetting(index, (int32_t)fval, false);
      }
    }
  }

  // ---------- Itho remote queries ----------
  if (root["ithoremotes"].is<bool>() && root["ithoremotes"].as<bool>())
  {
    jsonWsSend("remotes");
    sysStatReq = true;
  }
  if (root["ithovremotes"].is<bool>() && root["ithovremotes"].as<bool>())
  {
    jsonWsSend("vremotes");
    sysStatReq = true;
  }

  // "vremote" => use ithoI2CCommand (not available in RF standalone mode)
  if (root["vremote"].is<uint8_t>() && root["command"].is<const char *>())
  {
    if (systemConfig.itho_rf_standalone != 1)
      ithoI2CCommand(root["vremote"].as<uint8_t>(), root["command"].as<const char *>(), WEB);
  }
  // "remote" => use ithoExecRFCommand
  else if (root["remote"].is<uint8_t>() && root["command"].is<const char *>())
  {
    const char *cmd = root["command"].as<const char *>();
    if (strcmp(cmd, "join") == 0)
      bindInitiatorResult = 0; // reset before join
    ithoExecRFCommand(root["remote"].as<uint8_t>(), cmd, WEB);
  }
  // Poll bind initiator result
  if (!root["get_bind_result"].isNull())
  {
    JsonDocument doc;
    doc["bind_result"] = bindInitiatorResult; // 0=pending, 1=success, -1=timeout
    char buf[64]{};
    serializeJson(doc, buf, sizeof(buf));
    notifyClients(buf);
  }
  // Single top-level "command"
  else if (root["command"].is<const char *>())
  {
    ithoExecCommand(root["command"].as<const char *>(), WEB);
    sysStatReq = true;
  }
  // RF CO2 value command
  if (!root["rfco2"].isNull())
  {
    uint8_t idx = 0;
    if (root["rfremoteindex"].is<uint8_t>())
      idx = root["rfremoteindex"].as<uint8_t>();
    ithoSendRFCO2(idx, root["rfco2"].as<uint16_t>(), WEB);
  }
  // RF demand command
  if (!root["rfdemand"].isNull())
  {
    uint8_t idx = 0;
    if (root["rfremoteindex"].is<uint8_t>())
      idx = root["rfremoteindex"].as<uint8_t>();
    uint8_t zone = 0;
    if (root["rfzone"].is<uint8_t>())
      zone = root["rfzone"].as<uint8_t>();
    ithoSendRFDemand(idx, root["rfdemand"].as<uint8_t>(), zone, WEB);
  }
  // Percentage / fandemand command (unified fan control)
  if (!root["percentage"].isNull() || !root["fandemand"].isNull())
  {
    int demand = 0;
    if (!root["percentage"].isNull())
    {
      int pct = root["percentage"].as<int>();
      demand = (pct < 0) ? 0 : (pct > 100) ? 200 : pct * 2;
    }
    else
    {
      demand = root["fandemand"].as<int>();
      if (demand < 0) demand = 0;
      if (demand > 200) demand = 200;
    }

    if (systemConfig.itho_control_interface == 1)
    {
      // The RFT CO2 unit only accepts a 31E0 demand frame when in auto
      // mode. If FanInfo confirms it's already in auto, send only the
      // demand (this avoids the boost-mode side-effect that drops
      // subsequent lower demand values). Otherwise send "auto" first
      // to switch the unit to auto, then the demand.
      for (int ri = 0; ri < remotes.getMaxRemotes(); ri++)
      {
        if (remotes.isEmptySlot(ri)) continue;
        if (remotes.getRemoteFunction(ri) == RemoteFunctions::SEND &&
            remotes.getRemoteType(ri) == RemoteTypes::RFTCO2)
        {
          if (!fanIsInAuto())
          {
            ithoExecRFCommand(ri, "auto", WEB);
            delay(200);
          }
          ithoSendRFDemand(ri, (uint8_t)demand, 0, WEB);
          break;
        }
      }
    }
    else if (systemConfig.itho_pwm2i2c == 1)
    {
      ithoSetSpeed((uint16_t)((demand * 255) / 200), WEB);
    }
  }
  // Itho speed command
  if (root["itho"].is<uint16_t>())
  {
    ithoSetSpeed(root["itho"].as<uint16_t>(), WEB);
  }
  // Learn-Leave mode toggle
  if (root["itho_llm"].is<bool>() && root["itho_llm"].as<bool>())
  {
    toggleRemoteLLmode("remote");
  }

  // copy_id => for virtualRemotes
  if (root["copy_id"].is<bool>() && root["copy_id"].as<bool>())
  {
    int number = root["index"].as<uint8_t>();
    if (number > 0 && number <= virtualRemotes.getMaxRemotes())
    {
      virtualRemotes.copy_id_remote_idx = number - 1;
      toggleRemoteLLmode("vremote");
    }
  }

  // OTA update from online resource
  if (!root["update_url"].isNull())
  {
    const char *url = root["update_url"] | "";
    if (strncmp(url, "https://github.com/arjenhiemstra/ithowifi/", 42) == 0)
      triggerOTAUpdateFromURL(url);
  }
  else if (!root["update"].isNull() && root["update"].is<const char *>())
  {
    const char *value = root["update"] | "stable";
    bool beta = (strcmp(value, "beta") == 0);
    triggerOTAUpdate(beta);
  }

  // Removing or updating rf remote
  if (root["itho_remove_remote"].is<int>())
  {
    int index = root["itho_remove_remote"].as<int>();
    if (index > 0 && index <= remotes.getMaxRemotes())
    {
      remotes.removeRemote(index - 1);
      saveRemotesflag = true;
    }
  }
  if (root["itho_update_remote"].is<uint8_t>())
  {
    uint8_t idx = root["itho_update_remote"].as<uint8_t>();

    // name
    const char *val = root["value"].is<const char *>() ? root["value"].as<const char *>() : "";
    remotes.updateRemoteName(idx, val);

    // function
    auto remfunc = (RemoteFunctions)(root["remfunc"].is<uint8_t>() ? root["remfunc"].as<uint8_t>() : 0);
    remotes.updateRemoteFunction(idx, remfunc);

    // type
    auto rtype = (RemoteTypes)(root["remtype"].is<uint16_t>() ? root["remtype"].as<uint16_t>() : 0);
    remotes.updateRemoteType(idx, rtype);

    // bidirectional - derived from remote type
    bool bidir = (rtype == RemoteTypes::RFTAUTON || rtype == RemoteTypes::RFTN ||
                  rtype == RemoteTypes::RFTCO2 || rtype == RemoteTypes::RFTRV ||
                  rtype == RemoteTypes::RFTSPIDER);
    remotes.updateRemoteBidirectional(idx, bidir);

    // id array
    if (root["id"].is<JsonArray>())
    {
      JsonArray arr = root["id"].as<JsonArray>();
      if (arr.size() >= 3)
      {
        uint8_t id0 = arr[0].as<uint8_t>();
        uint8_t id1 = arr[1].as<uint8_t>();
        uint8_t id2 = arr[2].as<uint8_t>();
        remotes.updateRemoteID(idx, id0, id1, id2);
        rfManager.radio.updateRFDevice(idx, id0, id1, id2, remotes.getRemoteType(idx), bidir);
        // For Send remotes, the ID is the sourceID (what we transmit as)
        if (remfunc == RemoteFunctions::SEND)
        {
          rfManager.radio.updateSourceID(id0, id1, id2, idx);
        }
        // updateRFDevice() resets destinationID to the slot's own ID. Re-apply
        // the persisted destinationID if one is stored, so a joined or
        // explicitly-configured slot doesn't lose its addressing every time
        // the user clicks Update on the RF Devices page.
        uint8_t destId[3]{};
        remotes.getRemoteDestIDbyIndex(idx, &destId[0]);
        if (destId[0] != 0 || destId[1] != 0 || destId[2] != 0)
        {
          rfManager.radio.updateDestinationID(destId[0], destId[1], destId[2], idx);
        }
      }
    }
    // TX power
    if (!root["tx_power"].isNull())
    {
      remotes.updateRemoteTxPower(idx, root["tx_power"].as<uint8_t>());
    }
    saveRemotesflag = true;
  }

  // Removing or updating virtual remote
  if (root["itho_remove_vremote"].is<int>())
  {
    int index = root["itho_remove_vremote"].as<int>();
    if (index > 0 && index <= virtualRemotes.getMaxRemotes())
    {
      virtualRemotes.removeRemote(index - 1);
      saveVremotesflag = true;
    }
  }
  if (root["itho_update_vremote"].is<uint8_t>())
  {
    uint8_t idx = root["itho_update_vremote"].as<uint8_t>();

    const char *val = root["value"].is<const char *>() ? root["value"].as<const char *>() : "";
    virtualRemotes.updateRemoteName(idx, val);

    int vtype = root["remtype"].is<int>() ? root["remtype"].as<int>() : 0;
    virtualRemotes.updateRemoteType(idx, vtype);

    // ID array
    if (root["id"].is<JsonArray>())
    {
      JsonArray arr = root["id"].as<JsonArray>();
      if (arr.size() >= 3)
      {
        virtualRemotes.updateRemoteID(idx,
                                      arr[0].as<uint8_t>(),
                                      arr[1].as<uint8_t>(),
                                      arr[2].as<uint8_t>());
      }
    }
    saveVremotesflag = true;
  }

  // update_rf_id => array of 3 bytes
  if (root["update_rf_id"].is<JsonArray>())
  {
    JsonArray arr = root["update_rf_id"].as<JsonArray>();
    if (arr.size() >= 3)
    {
      uint8_t id0 = arr[0].as<uint8_t>();
      uint8_t id1 = arr[1].as<uint8_t>();
      uint8_t id2 = arr[2].as<uint8_t>();
      if (id0 == 0 && id1 == 0 && id2 == 0)
      {
        systemConfig.module_rf_id[0] = sys.getMac(3);
        systemConfig.module_rf_id[1] = sys.getMac(4);
        systemConfig.module_rf_id[2] = sys.getMac(5) - 1;
      }
      else
      {
        systemConfig.module_rf_id[0] = id0;
        systemConfig.module_rf_id[1] = id1;
        systemConfig.module_rf_id[2] = id2;
      }
      rfManager.radio.setDefaultID(systemConfig.module_rf_id[0],
                                   systemConfig.module_rf_id[1],
                                   systemConfig.module_rf_id[2]);
      saveSystemConfigflag = true;
    }
  }

  // Reboot
  if (root["reboot"].is<bool>())
  {
    shouldReboot = root["reboot"].as<bool>();
  }

  // Misc config flags
  if (root["saveallconfigs"].is<bool>() && root["saveallconfigs"].as<bool>())
  {
    saveAllConfigsflag = true;
  }
  if (root["resetwificonf"].is<bool>() && root["resetwificonf"].as<bool>())
  {
    resetWifiConfigflag = true;
  }
  if (root["resetsysconf"].is<bool>() && root["resetsysconf"].as<bool>())
  {
    resetSystemConfigflag = true;
  }
  if (root["resethadconf"].is<bool>() && root["resethadconf"].as<bool>())
  {
    resetHADiscConfigflag = true;
  }
  if (root["format"].is<bool>() && root["format"].as<bool>())
  {
    formatFileSystem = true;
  }

  // RF debug
  if (root["rfdebug"].is<uint16_t>())
  {
    uint16_t val = root["rfdebug"].as<uint16_t>();
    if (val == 0x31DA)
    {
      if (root["faninfo"].is<uint8_t>())
        faninfo31DA = root["faninfo"].as<uint8_t>();
      if (root["timer"].is<uint8_t>())
        timer31DA = root["timer"].as<uint8_t>();
      send31DAdebug = true;
    }
    else if (val == 0x31D9)
    {
      if (root["status"].is<uint8_t>())
      {
        status31D9 = root["status"].as<uint8_t>() * 2;
      }
      if (root["fault"].is<bool>())
        fault31D9 = root["fault"].as<bool>();
      if (root["frost"].is<bool>())
        frost31D9 = root["frost"].as<bool>();
      if (root["filter"].is<bool>())
        filter31D9 = root["filter"].as<bool>();
      send31D9debug = true;
    }
  }

  // Debug page: one-shot 31DA + 31D9 RF status request, sent from a
  // user-selected RF remote slot. The Itho only answers when the slot
  // is bi-directional and joined — for any other slot the request goes
  // out but the Itho ignores it. No bidirectional check here so the
  // debug page can be used to verify behaviour either way.
  if (root["rfstatusrequest"].is<bool>() && root["rfstatusrequest"].as<bool>())
  {
    uint8_t idx = 0;
    if (root["remote"].is<uint8_t>())
      idx = root["remote"].as<uint8_t>();

    // Optional dest_id override: 3-byte array. Lets the debug page
    // target a specific Itho address without modifying the saved
    // slot config — useful when the slot was never actually joined.
    uint8_t dest[3] = {0, 0, 0};
    const uint8_t *destPtr = nullptr;
    if (root["dest_id"].is<JsonArray>())
    {
      JsonArray arr = root["dest_id"].as<JsonArray>();
      if (arr.size() == 3)
      {
        dest[0] = arr[0].as<uint8_t>();
        dest[1] = arr[1].as<uint8_t>();
        dest[2] = arr[2].as<uint8_t>();
        destPtr = dest;
      }
    }

    // Optional opcode selector. Default (missing/unknown) = send both,
    // preserving backward compat for callers that only know about the
    // paired path. The debug page sets "31DA" or "31D9" so the user
    // can probe one opcode at a time.
    const char *opcode = root["opcode"] | "";
    if (strcmp(opcode, "31DA") == 0)
      sendRF31DARequest(idx, destPtr);
    else if (strcmp(opcode, "31D9") == 0)
      sendRF31D9Request(idx, destPtr);
    else
      sendRFStatusRequest(idx, destPtr);
  }

  // I2C sniffer
  if (root["i2csniffer"].is<uint8_t>())
  {
    auto *sg = static_cast<i2c_safe_guard_t *>(i2cManager.safe_guard);
    uint8_t val = root["i2csniffer"].as<uint8_t>();
    if (val == 1)
    {
      sg->sniffer_enabled = true;
      sg->sniffer_web_enabled = true;
      i2cSnifferEnable();
    }
    else
    {
      sg->sniffer_enabled = false;
      sg->sniffer_web_enabled = false;
      i2cSnifferDisable();
    }
  }
}
void onWsEvent(AsyncWebSocket *server, AsyncWebSocketClient *client, AwsEventType type, void *arg, uint8_t *data, size_t len)
{
  if (!client->id())
    return;

  if (type == WS_EVT_CONNECT)
  {
    client->setCloseClientOnQueueFull(false);
    return;
  }
  else if (type == WS_EVT_DISCONNECT)
  {
    xSemaphoreTake(g_wsBuffersMutex, portMAX_DELAY);
    g_wsBuffers.erase(client->id());
    xSemaphoreGive(g_wsBuffersMutex);
  }
  else if (type == WS_EVT_ERROR)
  {
    xSemaphoreTake(g_wsBuffersMutex, portMAX_DELAY);
    g_wsBuffers.erase(client->id());
    xSemaphoreGive(g_wsBuffersMutex);
  }
  else if (type == WS_EVT_PONG)
  {
    // Serial.printf("ws[%s][%u] pong[%u]: %s\n", server->url(), client->id(), len, (len)?(char*)data:"");
  }

  else if (type == WS_EVT_DATA)
  {

    AwsFrameInfo *info = (AwsFrameInfo *)arg;

    // info->index == 0 => this is the beginning of a new message
    if (info->index == 0)
    {
      // Clear (or create) the buffer for this client
      xSemaphoreTake(g_wsBuffersMutex, portMAX_DELAY);
      g_wsBuffers[client->id()].clear();
      xSemaphoreGive(g_wsBuffersMutex);
    }

    // Append this frame’s data if opcode == WS_TEXT
    if (info->opcode == WS_TEXT)
    {

      xSemaphoreTake(g_wsBuffersMutex, portMAX_DELAY);
      auto &msgBuffer = g_wsBuffers[client->id()];
      msgBuffer.append(reinterpret_cast<char *>(data), len);
      xSemaphoreGive(g_wsBuffersMutex);

      size_t currentSize = info->index + len;

      // If this is the final frame, we parse the entire message
      if (currentSize >= info->len)
      {
        xSemaphoreTake(g_wsBuffersMutex, portMAX_DELAY);
        std::string msgCopy = g_wsBuffers[client->id()];
        g_wsBuffers[client->id()].clear();
        xSemaphoreGive(g_wsBuffersMutex);

        JsonDocument wsDoc;
        auto error = deserializeJson(wsDoc, msgCopy);
        bool wasPing = (!error) ? false : (msgCopy == "ping");
        msgCopy.clear(); // free memory immediately after parsing

        if (error)
        {
          if (wasPing)
          {
            client->text("pong");
          }
          else
          {
            E_LOG("WEB: error - [WS] JSON parse error: %s", error.c_str());
          }
        }

        // if there was an error, we can now safely return (buffer is cleared)
        if (error)
          return;

        // Convert doc to a JsonObject
        JsonObject wsObj = wsDoc.as<JsonObject>();
        if (wsObj.isNull())
        {
          return;
        }
        handle_ws_message(wsObj);
      }
      else
      {
        // WS_TEXT partial frame handled, return to process the next message
        return;
      }

    }
  }
}
