arjenhiemstra/ithowifi/software/NRG_itho_wifi/main/tasks/task_cc1101.cpp

#include "tasks/task_cc1101.h"

#define TASK_CC1101_PRIO 5

// globals
Ticker TaskCC1101Timeout;
TaskHandle_t xTaskCC1101Handle = nullptr;
uint32_t TaskCC1101HWmark = 0;
bool send31D9 = false;
bool send31D9debug = false;
bool send31DAdebug = false;
uint8_t status31D9{0};
bool fault31D9 = false;
bool frost31D9 = false;
bool filter31D9 = false;
bool send31DA = false;
bool sendJoinReply = false;
bool send10E0 = false;
bool sendBindConfirm = false;
bool sendBatteryStatus = false;
uint8_t bindConfirmRemIndex = 255;
uint8_t faninfo31DA{0};
uint8_t timer31DA{0};

// locals
StaticTask_t xTaskCC1101Buffer;
StackType_t xTaskCC1101Stack[STACK_SIZE];

Ticker timerLearnLeaveMode;
Ticker rf_message;
Ticker bindInitiatorTimeout;

volatile bool ithoCheck = false;
SemaphoreHandle_t isrSemaphore = NULL;

IRAM_ATTR void ITHOinterrupt()
{
  // Try to take the semaphore
  if (xSemaphoreTakeFromISR(isrSemaphore, NULL) == pdTRUE)
  {
    // ISR code here

    ithoCheck = rfManager.radio.receivePacket();

    // At the end, give back the semaphore
    xSemaphoreGiveFromISR(isrSemaphore, NULL);
  }
}

void disableRF_ISR()
{
  detachInterrupt(hardwareManager.itho_irq_pin);
}

void enableRF_ISR()
{
  attachInterrupt(hardwareManager.itho_irq_pin, ITHOinterrupt, RISING);
  // If GDO is already HIGH, a packet arrived while the ISR was disabled.
  // The rising edge was missed, so manually trigger a receive.
  if (digitalRead(hardwareManager.itho_irq_pin) == HIGH)
  {
    ithoCheck = rfManager.radio.receivePacket();
  }
}

void RFDebug(IthoPacket *packet)
{
  char debugLog[400] = {0};
  strncat(debugLog, rfManager.radio.LastMessageDecoded(packet).c_str(), sizeof(debugLog) - strlen(debugLog) - 1);
  // log command
  switch (packet->command)
  {
  case IthoUnknown:
    strncat(debugLog, " (cmd:unknown)", sizeof(debugLog) - strlen(debugLog) - 1);
    break;
  case IthoAway:
    strncat(debugLog, " (cmd:away)", sizeof(debugLog) - strlen(debugLog) - 1);
    break;
  case IthoLow:
    strncat(debugLog, " (cmd:low)", sizeof(debugLog) - strlen(debugLog) - 1);
    break;
  case IthoMedium:
    strncat(debugLog, " (cmd:medium)", sizeof(debugLog) - strlen(debugLog) - 1);
    break;
  case IthoHigh:
    strncat(debugLog, " (cmd:high)", sizeof(debugLog) - strlen(debugLog) - 1);
    break;
  case IthoFull:
    strncat(debugLog, " (cmd:full)", sizeof(debugLog) - strlen(debugLog) - 1);
    break;
  case IthoAuto:
    strncat(debugLog, " (cmd:auto)", sizeof(debugLog) - strlen(debugLog) - 1);
    break;
  case IthoAutoNight:
    strncat(debugLog, " (cmd:autonight)", sizeof(debugLog) - strlen(debugLog) - 1);
    break;
  case IthoTimer1:
    strncat(debugLog, " (cmd:timer1)", sizeof(debugLog) - strlen(debugLog) - 1);
    break;
  case IthoTimer2:
    strncat(debugLog, " (cmd:timer2)", sizeof(debugLog) - strlen(debugLog) - 1);
    break;
  case IthoTimer3:
    strncat(debugLog, " (cmd:timer3)", sizeof(debugLog) - strlen(debugLog) - 1);
    break;
  case IthoCook30:
    strncat(debugLog, " (cmd:cook30)", sizeof(debugLog) - strlen(debugLog) - 1);
    break;
  case IthoCook60:
    strncat(debugLog, " (cmd:cook60)", sizeof(debugLog) - strlen(debugLog) - 1);
    break;
  case IthoTimerUser:
    strncat(debugLog, " (cmd:timeruser)", sizeof(debugLog) - strlen(debugLog) - 1);
    break;
  case IthoJoin:
    strncat(debugLog, " (cmd:join)", sizeof(debugLog) - strlen(debugLog) - 1);
    break;
  case IthoLeave:
    strncat(debugLog, " (cmd:leave)", sizeof(debugLog) - strlen(debugLog) - 1);
    break;
  case IthoJoinReply:
    strncat(debugLog, " (cmd:joinreply)", sizeof(debugLog) - strlen(debugLog) - 1);
    break;
  case IthoPIRmotionOn:
    strncat(debugLog, " (cmd:motion_on)", sizeof(debugLog) - strlen(debugLog) - 1);
    break;
  case IthoPIRmotionOff:
    strncat(debugLog, " (cmd:motion_off)", sizeof(debugLog) - strlen(debugLog) - 1);
    break;
  case Itho31D9:
    strncat(debugLog, " (cmd:itho31d9)", sizeof(debugLog) - strlen(debugLog) - 1);
    break;
  case Itho31DA:
    strncat(debugLog, " (cmd:itho31da)", sizeof(debugLog) - strlen(debugLog) - 1);
    break;
  case IthoDeviceInfo:
    strncat(debugLog, " (cmd:ithodeviceinfo)", sizeof(debugLog) - strlen(debugLog) - 1);
    break;
  case IthoBindAccept:
    strncat(debugLog, " (cmd:bindaccept)", sizeof(debugLog) - strlen(debugLog) - 1);
    break;
  case IthoBindConfirm:
    strncat(debugLog, " (cmd:bindconfirm)", sizeof(debugLog) - strlen(debugLog) - 1);
    break;
  }
  // strncat(debugLog, "\n", sizeof(debugLog) - strlen(debugLog) - 1);

  D_LOG(debugLog);

  logMessagejson(debugLog, RFLOG);
}

void toggleRemoteLLmode(const char *remotetype)
{

  if (strcmp(remotetype, "remote") == 0)
  {
    if (virtualRemotes.remoteLearnLeaveStatus())
    {
      logMessagejson("disable virtual remote Copy ID mode first", WEBINTERFACE);
      return;
    }
    if (remotes.toggleLearnLeaveMode())
    {
      // rfManager.radio.setBindAllowed(true);
      timerLearnLeaveMode.attach(1, setllModeTimer);
    }
    else
    {
      // rfManager.radio.setBindAllowed(false);
      timerLearnLeaveMode.detach();
      remotes.setllModeTime(0);
      sysStatReq = true;
    }
  }
  if (strcmp(remotetype, "vremote") == 0)
  {
    if (remotes.remoteLearnLeaveStatus())
    {
      logMessagejson("disable remote learn/leave mode first", WEBINTERFACE);
      return;
    }
    if (virtualRemotes.toggleLearnLeaveMode())
    {
      timerLearnLeaveMode.attach(1, setllModeTimer);
    }
    else
    {
      timerLearnLeaveMode.detach();
      virtualRemotes.setllModeTime(0);
      virtualRemotes.copy_id_remote_idx = -1;
      sysStatReq = true;
    }
  }
}

void setllModeTimer()
{

  if (remotes.remoteLearnLeaveStatus())
  {
    remotes.updatellModeTimer();
    sysStatReq = true;
    if (remotes.getllModeTime() == 0)
    {
      toggleRemoteLLmode("remote");
    }
    return;
  }
  if (virtualRemotes.remoteLearnLeaveStatus())
  {
    virtualRemotes.updatellModeTimer();
    sysStatReq = true;
    if (virtualRemotes.getllModeTime() == 0)
    {
      toggleRemoteLLmode("vremote");
    }
    return;
  }
}

volatile int8_t bindInitiatorResult = 0; // 0=idle, 1=success, -1=timeout

void bindInitiatorTimeoutCallback()
{
  if (rfManager.radio.isBindInitiatorActive())
  {
    rfManager.radio.setBindInitiatorActive(false);
    bindInitiatorResult = -1;
    W_LOG("RFI: Bind initiator timeout - no binding accept received");
  }
}

void startBindInitiatorTimeout()
{
  bindInitiatorTimeout.once_ms(5000, bindInitiatorTimeoutCallback);
}

void cancelBindInitiatorTimeout()
{
  bindInitiatorTimeout.detach();
}

void set_send10E0_true()
{
  send10E0 = true;
}
void set_send31D9_true()
{
  send31D9 = true;
}
void set_send31DA_true()
{
  send31DA = true;
}
void startTaskCC1101()
{
  xTaskCC1101Handle = xTaskCreateStaticPinnedToCore(
      TaskCC1101,
      "TaskCC1101",
      STACK_SIZE,
      (void *)1,
      TASK_CC1101_PRIO,
      xTaskCC1101Stack,
      &xTaskCC1101Buffer,
      CONFIG_ARDUINO_RUNNING_CORE);
}

void TaskCC1101(void *pvParameters)
{

  D_LOG("SYS: TaskCC1101 started");
  configASSERT((uint32_t)pvParameters == 1UL);

  if (!xTaskMQTTHandle)
    startTaskMQTT();

  // reading the chip version is a non-blocking way to check CC1101 connectivity.
  // if the version is greater than 0 there has been succesful communication and we can continue with the init of the chip.
  uint8_t chipVersion = rfManager.radio.getChipVersion();
  if (chipVersion)
  {
    N_LOG("SYS: CC1101 RF module found, chip version: 0x%02X", chipVersion);
  }
  else
  {
    N_LOG("SYS: no CC1101 RF module found");
    systemConfig.itho_rf_support = 0;
    systemConfig.rfInitOK = false;
  }
  if (systemConfig.itho_rf_support)
  {
    isrSemaphore = xSemaphoreCreateBinary();
    xSemaphoreGive(isrSemaphore);

    // init the RF module
    rfManager.radio.init();
    IthoCC1101::setRF31DACallback(parseRF31DA);
    IthoCC1101::setRF31D9Callback(parseRF31D9);
    if (systemConfig.module_rf_id[0] == 0 && systemConfig.module_rf_id[1] == 0 && systemConfig.module_rf_id[2] == 0)
    {
      systemConfig.module_rf_id[0] = sys.getMac(3);
      systemConfig.module_rf_id[1] = sys.getMac(4);
      systemConfig.module_rf_id[2] = sys.getMac(5) - 1;
      I_LOG("SYS: module_rf_id default 0x%02X,0x%02X,0x%02X", systemConfig.module_rf_id[0], systemConfig.module_rf_id[1], systemConfig.module_rf_id[2]);
      saveSystemConfigflag = true;
    }
    else
    {
      I_LOG("SYS: module_rf_id 0x%02X,0x%02X,0x%02X", systemConfig.module_rf_id[0], systemConfig.module_rf_id[1], systemConfig.module_rf_id[2]);
    }

    remotes.setMaxRemotes(systemConfig.itho_numrfrem);

    rfManager.radio.setDefaultID(systemConfig.module_rf_id[0], systemConfig.module_rf_id[1], systemConfig.module_rf_id[2]);
    rfManager.radio.setBindAllowed(false);
    rfManager.radio.setAllowAll(false);

    setRFdebugLevel(logConfig.rfloglevel);

    pinMode(hardwareManager.itho_irq_pin, INPUT);
    enableRF_ISR();

    systemConfig.itho_rf_support = 1;
    RemotesConfigLoaded = loadRemotesConfig("flash");
    for (int index = 0; index < remotes.getMaxRemotes(); index++)
    {
      if (remotes.isEmptySlot(index))
        continue;
      uint8_t id[3]{};
      remotes.getRemoteIDbyIndex(index, &id[0]);
      rfManager.radio.setBindAllowed(true);
      rfManager.radio.addRFDevice(id[0], id[1], id[2], remotes.getRemoteType(index), remotes.getRemoteBidirectional(index));
      rfManager.radio.setBindAllowed(false);
      // For Send remotes, set the sourceID to the configured ID (what we transmit as)
      if (remotes.getRemoteFunction(index) == RemoteFunctions::SEND)
      {
        rfManager.radio.updateSourceID(id[0], id[1], id[2], index);
      }
      // Restore persisted target device ID for bidirectional remotes
      uint8_t destId[3]{};
      remotes.getRemoteDestIDbyIndex(index, &destId[0]);
      if (destId[0] != 0 || destId[1] != 0 || destId[2] != 0)
      {
        rfManager.radio.updateDestinationID(destId[0], destId[1], destId[2], index);
      }
    }
    systemConfig.rfInitOK = true;
    // RF CO2 join on boot: find first Send+RFTCO2 remote and send join
    if (systemConfig.itho_rf_co2_join == 1)
    {
      for (int idx = 0; idx < remotes.getMaxRemotes(); idx++)
      {
        if (remotes.isEmptySlot(idx))
          continue;
        if (remotes.getRemoteFunction(idx) == RemoteFunctions::SEND &&
            remotes.getRemoteType(idx) == RemoteTypes::RFTCO2)
        {
          I_LOG("RFI: RF CO2 join on boot, remote index:%d", idx);
          ithoExecRFCommand(idx, "join", HTMLAPI);
          break;
        }
      }
      systemConfig.itho_rf_co2_join = 0;
      saveSystemConfigflag = true;
    }

    uint8_t joinReplyRemIndex{255};
    // uint8_t remIndex10E0{255};

    for (;;)
    {
      yield();
      esp_task_wdt_reset();

      TaskCC1101Timeout.once_ms(3000, []()
                                { W_LOG("SYS: warning - CC1101 Task timed out!"); });

      if (send10E0 && !ithoCheck)
      {
        send10E0 = false;
        rfManager.radio.setSendTries(1);
        disableRF_ISR();
        rfManager.radio.send10E0();
        enableRF_ISR();
        rfManager.radio.setSendTries(3);
        rf_message.once_ms(100, set_send31D9_true);
      }
      if (sendJoinReply && !ithoCheck)
      {
        /*

        H:18 _I P0:-- P1:-- 94,11,A9 --,--,-- 94,11,A9 1FC9 12:00,22,F8,94,11,A9,01,10,E0,94,11,A9,00,1F,C9,94,11,A9 (cmd:join)
        Join command received. Trying to join remote...
        ?? 13-10-2024, 15:55:59: H:1C _I P0:-- P1:-- 94,11,A9 96,C8,B6 --,--,-- 1FC9 01:00 (cmd:unknown)
        Send join reply
        H:2C _W P0:-- P1:-- 96,C8,B6 94,11,A9 --,--,-- 1FC9 0C:00,31,D9,96,C8,B6,00,31,DA,96,C8,B6 (cmd:unknown)
        receive battery
        H:18 _I P0:-- P1:-- 94,11,A9 --,--,-- 94,11,A9 1060 03:00,FF,01 (cmd:unknown)
        H:18 _I P0:-- P1:-- 94,11,A9 --,--,-- 94,11,A9 1060 03:00,FF,01 (cmd:unknown)
        send 10E0
        H:18 _I P0:-- P1:-- 96,C8,B6 --,--,-- 96,C8,B6 10E0 26:00,00,01,00,1B,31,19,01,FE,FF,FF,FF,FF,FF,0E,05,07,E2,43,56,45,2D,52,46,00,00,00,00,00,00,00,00,00,00,00,00,00,00 (cmd:unknown)
        send 31D9
        H:1A _I P0:02  P1:-- 96,C8,B6 --,--,-- 96,C8,B6 31D9 11:00,06,9A,00,20,20,20,20,20,20,20,20,20,20,20,20,00 (cmd:unknown)
        send 31D9
        H:1A _I P0:03  P1:-- 96,C8,B6 --,--,-- 96,C8,B6 31D9 11:00,06,C7,00,20,20,20,20,20,20,20,20,20,20,20,20,00 (cmd:unknown)
        receive command low
        H:1C _I P0:-- P1:-- 94,11,A9 96,C8,B6 --,--,-- 22F1 03:00,02,04 (cmd:low)
        send 31D9
        H:1A _I P0:04  P1:-- 96,C8,B6 --,--,-- 96,C8,B6 31D9 11:00,06,99,00,20,20,20,20,20,20,20,20,20,20,20,20,00 (cmd:unknown)
        send 31D9
        H:1A _I P0:05  P1:-- 96,C8,B6 --,--,-- 96,C8,B6 31D9 11:00,06,1F,00,20,20,20,20,20,20,20,20,20,20,20,20,00 (cmd:unknown)
        H:18 _I P0:-- P1:-- 96,C8,B6 --,--,-- 96,C8,B6 042F 01:00 (cmd:unknown)
        H:18 _I P0:-- P1:-- 96,C8,B6 --,--,-- 96,C8,B6 042F 09:00,FF,EA,21,D1,02,01,1B,70 (cmd:unknown)
        H:18 _I P0:-- P1:-- 96,C8,B6 --,--,-- 96,C8,B6 3120 07:00,70,B0,00,00,E9,FF (cmd:unknown)
        H:18 _I P0:-- P1:-- 96,C8,B6 --,--,-- 96,C8,B6 10E0 26:00,00,01,00,1B,31,19,01,FE,FF,FF,FF,FF,FF,0E,05,07,E2,43,56,45,2D,52,46,00,00,00,00,00,00,00,00,00,00,00,00,00,00 (cmd:unknown)
        H:18 _I P0:-- P1:-- 96,C8,B6 --,--,-- 96,C8,B6 04FF FF:18,96,C8,B6,96,C8,B6,04,FF,FF,FF,BE,F7,7F,FF,FF,FF,FF,F7,BD,FB,FB,FF,FF,9F,FF,FB,C6,FF,FF,DF,EE,FF,FF,FB,FF,DF,FF,FF,BF,5F,DF,F7,ED,F3,E7,DD,7F,F7,FB,FE,F7,F7,FF,FF,7D,FF,36,BE,D7,FE,F7,FF,FF,67,00,00,00,00,00,00,00,00,00,00,00,00,00,00,00,00,00,40,00,00,FD,97,E7,00,00,00,00,00,00,00,00,00,00,C0,00,00,00,00,00,00,00,00,00,00,00,00,00,00,00,00
        H:18 _I P0:-- P1:-- 96,C8,B6 --,--,-- 96,C8,B0 0000 0F:FF,EF,FF,FF,7F,FF,FF,F7,FF,D7,DF,FF,BF,F7,FF (cmd:unknown)

        */
        sendJoinReply = false;
        rfManager.radio.setSendTries(1);
        disableRF_ISR();
        int res = rfManager.radio.sendJoinReply(joinReplyRemIndex);
        enableRF_ISR();
        D_LOG("RFI: Join reply send, result:%d", res);
        rfManager.radio.setSendTries(3);
        joinReplyRemIndex = 255;
        rf_message.once_ms(100, set_send10E0_true);
      }
      if (sendBindConfirm && !ithoCheck)
      {
        /*
          Initiator binding flow:
          1. We sent the Binding Offer (1FC9 I, self-addressed)
          2. Target responded with Binding Accept (1FC9 W, 31D9+31DA)
          3. Now send Binding Confirm (1FC9 I, payload 00, addr0=us addr1=target)
          4. Then send Battery Status (1060 x3)
        */
        sendBindConfirm = false;
        rfManager.radio.setSendTries(3);
        disableRF_ISR();
        rfManager.radio.sendBindConfirm(bindConfirmRemIndex);
        enableRF_ISR();
        D_LOG("RFI: Bind confirm sent for remote index:%d", bindConfirmRemIndex);
        // Schedule battery status after a short delay
        sendBatteryStatus = true;
      }
      if (sendBatteryStatus && !ithoCheck)
      {
        sendBatteryStatus = false;
        rfManager.radio.setSendTries(3); // send 3 times for reliability
        disableRF_ISR();
        rfManager.radio.send1060();
        enableRF_ISR();
        D_LOG("RFI: Battery status (1060) sent");
        bindConfirmRemIndex = 255;
      }
      if ((send31D9 || send31D9debug) && !ithoCheck)
      {
        // 80 82 B1 D9 01 10 86 05 0A 20 20 20 20 20 20 20 20 20 20 20 20 00 4E
        uint8_t command[] = {0x31, 0xD9, 0x11, 0x00, 0x06, 0x00, 0x0A, 0x20, 0x20, 0x20, 0x20, 0x20, 0x20, 0x20, 0x20, 0x20, 0x20, 0x20, 0x20, 0x00};

        if (send31D9)
        {
          send31D9 = false;

          uint8_t receive_buffer[256]{};
          size_t result = sendQuery31D9(&receive_buffer[0]);

          if (result > 4)
          {
            for (uint8_t i = 4; i < sizeof(command); i++)
            {
              command[i] = receive_buffer[i + 2];
            }
          }
        }
        if (send31D9debug)
        {
          send31D9debug = false;
          uint8_t speedstatus = status31D9;
          uint8_t fanstate = 0;
          fanstate |= fault31D9 ? 0x80 : 0x00;
          fanstate |= frost31D9 ? 0x40 : 0x00;
          fanstate |= filter31D9 ? 0x20 : 0x00;
          command[5] = speedstatus;
          command[4] = fanstate;
        }
        rfManager.radio.setSendTries(1);
        disableRF_ISR();
        rfManager.radio.send31D9(&command[0]);
        enableRF_ISR();
        rfManager.radio.setSendTries(3);
      }
      if ((send31DA || send31DAdebug) && !ithoCheck)
      {
        uint8_t command[] = {0x31, 0xDA, 0x1D, 0x00, 0xC8, 0x40, 0xEF, 0x7F, 0xFF, 0x7F, 0xFF, 0x7F, 0xFF, 0x7F, 0xFF, 0x7F, 0xFF, 0xEF, 0xF8, 0x08, 0xEF, 0x00, 0x00, 0x00, 0x00, 0x00, 0xEF, 0xEF, 0x7F, 0xFF, 0x7F, 0xFF};

        if (send31DA)
        {
          send31DA = false;

          uint8_t receive_buffer[256]{};
          size_t result = sendQuery31DA(&receive_buffer[0]);
          // 80 82 B1 DA 01 1C C8 40 03 A5 39 EF 7F FF 7F FF 7F FF 7F FF F8 08 EF 98 05 00 00 00 EF EF 7F FF 7F FF 20
          // 1D:            00,C8,40,04,7B,38,EF,7F,FF,7F,FF,7F,FF,7F,FF,F8,08,EF,98,05,00,00,00,EF,EF,7F,FF,7F,FF

          if (result > 4)
          {
            for (uint8_t i = 4; i < sizeof(command); i++)
            {
              command[i] = receive_buffer[i + 2];
            }
          }
          else
          {
            E_LOG("I2C: error - sendQuery31DA failed");
          }
        }
        if (send31DAdebug)
        {
          send31DAdebug = false;

          command[21] = faninfo31DA;
          command[24] = timer31DA;
        }

        rfManager.radio.setSendTries(1);
        disableRF_ISR();
        rfManager.radio.send31DA(&command[0]);
        enableRF_ISR();
        rfManager.radio.setSendTries(3);
      }
      if (ithoCheck)
      {
        ithoCheck = false;

        rfManager.radio.decodeBufferedPacket();
        IthoPacket *packet = rfManager.radio.checkForNewPacket();
        rfManager.radio.parseMessage(packet);

        uint8_t *lastID = rfManager.radio.getLastID(packet);
        IthoCommand cmd = rfManager.radio.getLastCommand(packet);
        RemoteTypes remtype = rfManager.radio.getLastRemType(packet);
        bool chk = remotes.checkID(*(lastID + 0), *(lastID + 1), *(lastID + 2));
        if (logConfig.rfloglevel >= 2)
        {
          if (chk || logConfig.rfloglevel == 3)
          {
            RFDebug(packet);
          }
        }
        if (cmd != IthoUnknown)
        { // only act on good cmd
          if (logConfig.rfloglevel == 1)
          {
            RFDebug(packet);
          }
          if (cmd == IthoLeave && remotes.remoteLearnLeaveStatus())
          {
            D_LOG("RFI: Leave command received. Trying to remove remote...");
            int index = remotes.removeRemote(*(lastID + 0), *(lastID + 1), *(lastID + 2));
            if (index >= 0)
            {
              rfManager.radio.removeRFDevice(index);
            }
            switch (index)
            {
            case -1: // failed! - remote not registered
              break;
            case -2: // failed! - no remotes registered
              break;
            case 1: // success!
              saveRemotesflag = true;
              break;
            }
          }
          if (cmd == IthoBindAccept)
          {
            cancelBindInitiatorTimeout();
            bindInitiatorResult = 1;
            uint8_t remIdx = rfManager.radio.getBindInitiatorRemIndex();
            D_LOG("RFI: Binding accept received, remote index:%d", remIdx);
            // Store the target's device ID as the destination for this remote (runtime)
            rfManager.radio.updateDestinationID(*(lastID + 0), *(lastID + 1), *(lastID + 2), remIdx);
            // Persist the target device ID so it survives reboot
            remotes.updateRemoteDestID(remIdx, *(lastID + 0), *(lastID + 1), *(lastID + 2));
            saveRemotesflag = true;
            bindConfirmRemIndex = remIdx;
            // Auto-switch to RF CO2 control interface if this is an RFTCO2 send remote
            if (remotes.getRemoteType(remIdx) == RemoteTypes::RFTCO2 &&
                remotes.getRemoteFunction(remIdx) == RemoteFunctions::SEND)
            {
              systemConfig.itho_control_interface = 1;
              saveSystemConfigflag = true;
              I_LOG("RFI: RF CO2 join successful, control interface set to RF CO2");
            }
            // Auto-track the Itho device as RF status source for 31DA/31D9 data
            if (remotes.getRemoteFunction(remIdx) == RemoteFunctions::SEND)
            {
              rfStatusSource *src = findOrAllocRFStatusSource(*(lastID + 0), *(lastID + 1), *(lastID + 2));
              if (src && !src->tracked)
              {
                src->tracked = true;
                const char *remName = remotes.getRemoteNamebyIndex(remIdx);
                if (remName && strlen(remName) > 0)
                  strlcpy(src->name, remName, sizeof(src->name));
                else
                  strlcpy(src->name, "Itho (auto)", sizeof(src->name));
                saveRFTrackedSources();
                I_LOG("RFI: Auto-tracked Itho device %02X:%02X:%02X as '%s'",
                      *(lastID + 0), *(lastID + 1), *(lastID + 2), src->name);
              }
            }
            // Delay the confirm to let the remaining accepts from the target pass
            rf_message.once_ms(300, []()
                               { sendBindConfirm = true; });
          }
          if (cmd == IthoJoin || (cmd == IthoLow && remtype == RemoteTypes::RFTSPIDER)) // Itho low for the spider because join can be difficult to send
          {
            D_LOG("RFI: Join command received. Trying to join remote...");
            if (remotes.remoteLearnLeaveStatus())
            {
              int index = remotes.registerNewRemote(*(lastID + 0), *(lastID + 1), *(lastID + 2), remtype);

              if (index == -1)
              {
                // Already registered — look up existing index for re-binding
                index = remotes.remoteIndex(*(lastID + 0), *(lastID + 1), *(lastID + 2));
                D_LOG("RFI: Remote already registered at index:%d, re-binding", index);
              }

              if (index >= 0)
              {
                // Auto-detect bidirectional from remote type (unless monitor mode)
                bool bidirectional = (remtype == RemoteTypes::RFTAUTON || remtype == RemoteTypes::RFTN ||
                                      remtype == RemoteTypes::RFTCO2 || remtype == RemoteTypes::RFTRV ||
                                      remtype == RemoteTypes::RFTSPIDER)
                                         ? (remotes.getRemoteFunction(index) != RemoteFunctions::MONITOR)
                                         : false;
                remotes.updateRemoteBidirectional(index, bidirectional);
                rfManager.radio.updateRFDevice(index, *(lastID + 0), *(lastID + 1), *(lastID + 2), remotes.getRemoteType(index), bidirectional);

                if (bidirectional)
                {
                  joinReplyRemIndex = index;
                  sendJoinReply = true;
                }
                else if (remotes.getRemoteFunction(index) == RemoteFunctions::MONITOR)
                {
                  D_LOG("RFI: Remote index:%d is monitor-only, not sending join reply", index);
                }

                saveRemotesflag = true;
              }
              // index == -2: max number of remotes reached
            }
            if (virtualRemotes.remoteLearnLeaveStatus())
            {
              int result = virtualRemotes.registerNewRemote(*(lastID + 0), *(lastID + 1), *(lastID + 2), remtype);
              D_LOG("RFI: registerNewRemote:%d", result);

              if (result >= 0)
              {
                saveVremotesflag = true;
                // delay(200);
                toggleRemoteLLmode("vremote");
              }
              else
              {
                // error
                // case -1: // failed! - remote already registered
                //   break;
                // case -2: // failed! - max number of remotes reached"
              }
            }
          }
          if (chk)
          {
            int index = remotes.remoteIndex(*(lastID + 0), *(lastID + 1), *(lastID + 2));
            remotes.lastRemoteName = remotes.getRemoteNamebyIndex(index);
            RemoteFunctions remfunc = remotes.getRemoteFunction(index);
            bool bidirect = remotes.getRemoteBidirectional(index);
            if (remfunc != RemoteFunctions::MONITOR)
            {
              D_LOG("RFI: remfunc:%d, bidirect:%s", remfunc, bidirect ? "yes" : "no");
              if (cmd == IthoLow)
              {
                ithoExecCommand("low", REMOTE);
              }
              if (cmd == IthoMedium)
              {
                ithoExecCommand("medium", REMOTE);
              }
              if (cmd == IthoHigh)
              {
                ithoExecCommand("high", REMOTE);
              }
              if (cmd == IthoTimer1)
              {
                ithoExecCommand("timer1", REMOTE);
              }
              if (cmd == IthoTimer2)
              {
                ithoExecCommand("timer2", REMOTE);
              }
              if (cmd == IthoTimer3)
              {
                ithoExecCommand("timer3", REMOTE);
              }
              if (cmd == IthoCook30)
              {
                ithoExecCommand("cook30", REMOTE);
              }
              if (cmd == IthoCook60)
              {
                ithoExecCommand("cook60", REMOTE);
              }
              if (cmd == IthoAuto)
              {
                ithoExecCommand("auto", REMOTE);
              }
              if (cmd == IthoAutoNight)
              {
                ithoExecCommand("autonight", REMOTE);
              }
              if (cmd == IthoJoin && !remotes.remoteLearnLeaveStatus())
              {
              }
              if (cmd == IthoLeave && !remotes.remoteLearnLeaveStatus())
              {
                ithoQueue.clearQueue();
              }
              if (cmd == Itho31D9)
              {
                // send31D9 = true;
              }
              if (cmd == Itho31DA)
              {
                // send31DA = true;
              }
              if (cmd == IthoDeviceInfo)
              {
                // send10E0 = true;
              }
              if (bidirect && (cmd != IthoJoin && cmd != IthoLeave))
              { // trigger fan status update if there is a bi-directional remote in the known list of remotes
                // rf_message.once_ms(100, set_send31D9_true);
                rf_message.once_ms(150, set_send31DA_true);
                // send31D9 = true;
                // send31DA = true;
              }
            }
          }
          else
          {
            // Unknown remote
          }
        }
        else
        {
          //("--- RF CMD reveiced but of unknown type ---");
        }

        const ithoRFDevices &rfDevices = rfManager.radio.getRFdevices();
        for (auto &item : rfDevices.device)
        {
          if (item.destinationID[0] == 0 && item.destinationID[1] == 0 && item.destinationID[2] == 0)
            continue;
          // if (item.bidirectional && (cmd != IthoJoin && cmd != IthoLeave))
          // { // trigger fan status update if there is a bi-directional remote in the known list of remotes
          //   send31D9 = true;
          //   send31DA = true;
          // }
          int remIndex = remotes.remoteIndex(item.destinationID[0], item.destinationID[1], item.destinationID[2]);
          if (remIndex >= 0)
          {
            remotes.addCapabilities(remIndex, "timestamp", item.timestamp);
            remotes.addCapabilities(remIndex, "lastcmd", item.lastCommand);
            if (item.co2 != 0xEFFF)
            {
              remotes.addCapabilities(remIndex, "co2", item.co2);
            }
            if (item.temp != 0xEFFF)
            {
              remotes.addCapabilities(remIndex, "temp", item.temp);
            }
            if (item.hum != 0xEFFF)
            {
              remotes.addCapabilities(remIndex, "hum", item.hum);
            }
            if (item.dewpoint != 0xEFFF)
            {
              remotes.addCapabilities(remIndex, "dewpoint", item.dewpoint);
            }
            if (item.battery != 0xEFFF)
            {
              remotes.addCapabilities(remIndex, "battery", item.battery);
            }
            if (item.pir != 0xEF)
            {
              remotes.addCapabilities(remIndex, "pir", item.pir);
            }
            if (item.setpoint != 0xEFFF)
            {
              remotes.addCapabilities(remIndex, "setpoint", item.setpoint);
            }
            //
          }
        }
        //} //while
      }
      TaskCC1101HWmark = uxTaskGetStackHighWaterMark(NULL);
      vTaskDelay(25 / portTICK_PERIOD_MS);
    }
  } // if (systemConfig.itho_rf_support)
  // else delete task
  TaskHandle_t xTempTask = xTaskCC1101Handle;
  xTaskCC1101Handle = NULL;
  vTaskDelete(xTempTask);
}
