arjenhiemstra/ithowifi/software/NRG_itho_wifi/main/ithodevice/IthoDevice.cpp

#include "IthoDevice.h"

#include "devices/cve14.h"
#include "devices/cve1B.h"
#include "devices/hru200.h"
#include "devices/hru250_300.h"
#include "devices/hru350.h"
#include "devices/hrueco.h"
#include "devices/demandflow.h"
#include "devices/autotemp.h"
#include "devices/wpu.h"

uint8_t ithoDeviceGroup = 0;
uint8_t ithoDeviceID = 0;
uint8_t itho_hwversion = 0;
uint8_t itho_fwversion = 0;
volatile uint16_t ithoCurrentVal = 0;
volatile uint8_t ithoFanDemand = 0;
const struct ihtoDeviceType *ithoDeviceptr = nullptr;
int16_t ithoSettingsLength = 0;
int16_t ithoStatusLabelLength = 0;

struct lastCommand lastCmd;

const std::map<cmdOrigin, const char *> cmdOriginMap = {
    {cmdOrigin::HTMLAPI, "HTML API"},
    {cmdOrigin::MQTTAPI, "MQTT API"},
    {cmdOrigin::REMOTE, "remote"},
    {cmdOrigin::WEB, "web interface"},
    {cmdOrigin::UNKNOWN, "unknown"}};

const struct ihtoDeviceType ithoDevices[]{
    {0x00, 0x01, "Air curtain", nullptr, 0, nullptr, nullptr, 0, nullptr},
    {0x00, 0x03, "HRU ECO-fan", ithoHRUecoFanSettingsMap, sizeof(ithoHRUecoFanSettingsMap) / sizeof(ithoHRUecoFanSettingsMap[0]), ithoHRUecoSettingsLabels, ithoHRUecoFanStatusMap, sizeof(ithoHRUecoFanStatusMap) / sizeof(ithoHRUecoFanStatusMap[0]), ithoHRUecoStatusLabels},
    {0x00, 0x04, "CVE ECO2", nullptr, 0, nullptr, nullptr, 0, nullptr},
    {0x00, 0x08, "LoadBoiler", nullptr, 0, nullptr, nullptr, 0, nullptr},
    {0x00, 0x0A, "GGBB", nullptr, 0, nullptr, nullptr, 0, nullptr},
    {0x00, 0x0B, "DemandFlow", ithoDemandFlowSettingsMap, sizeof(ithoDemandFlowSettingsMap) / sizeof(ithoDemandFlowSettingsMap[0]), ithoDemandFlowSettingsLabels, ithoDemandFlowStatusMap, sizeof(ithoDemandFlowStatusMap) / sizeof(ithoDemandFlowStatusMap[0]), ithoDemandFlowStatusLabels},
    {0x00, 0x0C, "CO2 relay", nullptr, 0, nullptr, nullptr, 0, nullptr},
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
